farisrfp/smart-pju-device/firmware/interface/pnpm-lock.yaml

lockfileVersion: '6.0'

dependencies:
  '@emotion/react':
    specifier: ^11.7.1
    version: 11.7.1(@babel/core@7.22.1)(react@17.0.2)
  '@emotion/styled':
    specifier: ^11.6.0
    version: 11.6.0(@babel/core@7.22.1)(@emotion/react@11.7.1)(react@17.0.2)
  '@fseehawer/react-circular-slider':
    specifier: ^2.6.1
    version: 2.6.1(global@4.4.0)(react-dom@17.0.2)(react@17.0.2)
  '@headlessui/react':
    specifier: ^1.7.15
    version: 1.7.15(react-dom@17.0.2)(react@17.0.2)
  '@heroicons/react':
    specifier: ^2.0.18
    version: 2.0.18(react@17.0.2)
  '@mui/icons-material':
    specifier: ^5.11.16
    version: 5.11.16(@mui/material@5.2.4)(react@17.0.2)
  '@mui/material':
    specifier: ^5.2.4
    version: 5.2.4(@emotion/react@11.7.1)(@emotion/styled@11.6.0)(react-dom@17.0.2)(react@17.0.2)
  '@testing-library/jest-dom':
    specifier: ^5.16.1
    version: 5.16.1
  '@testing-library/react':
    specifier: ^12.1.2
    version: 12.1.2(react-dom@17.0.2)(react@17.0.2)
  '@testing-library/user-event':
    specifier: ^13.5.0
    version: 13.5.0(@testing-library/dom@9.3.0)
  axios:
    specifier: ^0.27.2
    version: 0.27.2
  react:
    specifier: ^17.0.2
    version: 17.0.2
  react-dom:
    specifier: ^17.0.2
    version: 17.0.2(react@17.0.2)
  react-router-dom:
    specifier: '6'
    version: 6.0.0(react-dom@17.0.2)(react@17.0.2)
  react-scripts:
    specifier: 5.0.0
    version: 5.0.0(@babel/plugin-syntax-flow@7.21.4)(@babel/plugin-transform-react-jsx@7.22.3)(eslint@8.42.0)(react@17.0.2)(typescript@5.1.3)
  replace:
    specifier: ^1.2.1
    version: 1.2.1
  web-vitals:
    specifier: ^2.1.2
    version: 2.1.2
  websocket:
    specifier: ^1.0.34
    version: 1.0.34

devDependencies:
  prettier:
    specifier: ^2.8.8
    version: 2.8.8
  prettier-plugin-tailwindcss:
    specifier: ^0.3.0
    version: 0.3.0(prettier@2.8.8)
  tailwindcss:
    specifier: ^3.3.2
    version: 3.3.2

packages:

  /@alloc/quick-lru@5.2.0:
    resolution: {integrity: sha512-UrcABB+4bUrFABwbluTIBErXwvbsU/V7TZWfmbgJfbkwiBuziS9gxdODUyuiecfdGQ85jglMW6juS3+z5TsKLw==}
    engines: {node: '>=10'}

  /@ampproject/remapping@2.2.1:
    resolution: {integrity: sha512-lFMjJTrFL3j7L9yBxwYfCq2k6qqwHyzuUl/XBnif78PWTJYyL/dfowQHWE3sp6U6ZzqWiiIZnpTMO96zhkjwtg==}
    engines: {node: '>=6.0.0'}
    dependencies:
      '@jridgewell/gen-mapping': 0.3.3
      '@jridgewell/trace-mapping': 0.3.18
    dev: false

  /@apideck/better-ajv-errors@0.3.6(ajv@8.12.0):
    resolution: {integrity: sha512-P+ZygBLZtkp0qqOAJJVX4oX/sFo5JR3eBWwwuqHHhK0GIgQOKWrAfiAaWX0aArHkRWHMuggFEgAZNxVPwPZYaA==}
    engines: {node: '>=10'}
    peerDependencies:
      ajv: '>=8'
    dependencies:
      ajv: 8.12.0
      json-schema: 0.4.0
      jsonpointer: 5.0.1
      leven: 3.1.0
    dev: false

  /@babel/code-frame@7.21.4:
    resolution: {integrity: sha512-LYvhNKfwWSPpocw8GI7gpK2nq3HSDuEPC/uSYaALSJu9xjsalaaYFOq0Pwt5KmVqwEbZlDu81aLXwBOmD/Fv9g==}
    engines: {node: '>=6.9.0'}
    dependencies:
      '@babel/highlight': 7.18.6
    dev: false

  /@babel/compat-data@7.22.3:
    resolution: {integrity: sha512-aNtko9OPOwVESUFp3MZfD8Uzxl7JzSeJpd7npIoxCasU37PFbAQRpKglkaKwlHOyeJdrREpo8TW8ldrkYWwvIQ==}
    engines: {node: '>=6.9.0'}
    dev: false

  /@babel/core@7.22.1:
    resolution: {integrity: sha512-Hkqu7J4ynysSXxmAahpN1jjRwVJ+NdpraFLIWflgjpVob3KNyK3/tIUc7Q7szed8WMp0JNa7Qtd1E9Oo22F9gA==}
    engines: {node: '>=6.9.0'}
    dependencies:
      '@ampproject/remapping': 2.2.1
      '@babel/code-frame': 7.21.4
      '@babel/generator': 7.22.3
      '@babel/helper-compilation-targets': 7.22.1(@babel/core@7.22.1)
      '@babel/helper-module-transforms': 7.22.1
      '@babel/helpers': 7.22.3
      '@babel/parser': 7.22.4
      '@babel/template': 7.21.9
      '@babel/traverse': 7.22.4
      '@babel/types': 7.22.4
      convert-source-map: 1.9.0
      debug: 4.3.4
      gensync: 1.0.0-beta.2
      json5: 2.2.3
      semver: 6.3.0
    transitivePeerDependencies:
      - supports-color
    dev: false

  /@babel/eslint-parser@7.21.8(@babel/core@7.22.1)(eslint@8.42.0):
    resolution: {integrity: sha512-HLhI+2q+BP3sf78mFUZNCGc10KEmoUqtUT1OCdMZsN+qr4qFeLUod62/zAnF3jNQstwyasDkZnVXwfK2Bml7MQ==}
    engines: {node: ^10.13.0 || ^12.13.0 || >=14.0.0}
    peerDependencies:
      '@babel/core': '>=7.11.0'
      eslint: ^7.5.0 || ^8.0.0
    dependencies:
      '@babel/core': 7.22.1
      '@nicolo-ribaudo/eslint-scope-5-internals': 5.1.1-v1
      eslint: 8.42.0
      eslint-visitor-keys: 2.1.0
      semver: 6.3.0
    dev: false

  /@babel/generator@7.22.3:
    resolution: {integrity: sha512-C17MW4wlk//ES/CJDL51kPNwl+qiBQyN7b9SKyVp11BLGFeSPoVaHrv+MNt8jwQFhQWowW88z1eeBx3pFz9v8A==}
    engines: {node: '>=6.9.0'}
    dependencies:
      '@babel/types': 7.22.4
      '@jridgewell/gen-mapping': 0.3.3
      '@jridgewell/trace-mapping': 0.3.18
      jsesc: 2.5.2
    dev: false

  /@babel/helper-annotate-as-pure@7.18.6:
    resolution: {integrity: sha512-duORpUiYrEpzKIop6iNbjnwKLAKnJ47csTyRACyEmWj0QdUrm5aqNJGHSSEQSUAvNW0ojX0dOmK9dZduvkfeXA==}
    engines: {node: '>=6.9.0'}
    dependencies:
      '@babel/types': 7.22.4
    dev: false

  /@babel/helper-builder-binary-assignment-operator-visitor@7.22.3:
    resolution: {integrity: sha512-ahEoxgqNoYXm0k22TvOke48i1PkavGu0qGCmcq9ugi6gnmvKNaMjKBSrZTnWUi1CFEeNAUiVba0Wtzm03aSkJg==}
    engines: {node: '>=6.9.0'}
    dependencies:
      '@babel/types': 7.22.4
    dev: false

  /@babel/helper-compilation-targets@7.22.1(@babel/core@7.22.1):
    resolution: {integrity: sha512-Rqx13UM3yVB5q0D/KwQ8+SPfX/+Rnsy1Lw1k/UwOC4KC6qrzIQoY3lYnBu5EHKBlEHHcj0M0W8ltPSkD8rqfsQ==}
    engines: {node: '>=6.9.0'}
    peerDependencies:
      '@babel/core': ^7.0.0
    dependencies:
      '@babel/compat-data': 7.22.3
      '@babel/core': 7.22.1
      '@babel/helper-validator-option': 7.21.0
      browserslist: 4.21.7
      lru-cache: 5.1.1
      semver: 6.3.0
    dev: false

  /@babel/helper-create-class-features-plugin@7.22.1(@babel/core@7.22.1):
    resolution: {integrity: sha512-SowrZ9BWzYFgzUMwUmowbPSGu6CXL5MSuuCkG3bejahSpSymioPmuLdhPxNOc9MjuNGjy7M/HaXvJ8G82Lywlw==}
    engines: {node: '>=6.9.0'}
    peerDependencies:
      '@babel/core': ^7.0.0
    dependencies:
      '@babel/core': 7.22.1
      '@babel/helper-annotate-as-pure': 7.18.6
      '@babel/helper-environment-visitor': 7.22.1
      '@babel/helper-function-name': 7.21.0
      '@babel/helper-member-expression-to-functions': 7.22.3
      '@babel/helper-optimise-call-expression': 7.18.6
      '@babel/helper-replace-supers': 7.22.1
      '@babel/helper-skip-transparent-expression-wrappers': 7.20.0
      '@babel/helper-split-export-declaration': 7.18.6
      semver: 6.3.0
    transitivePeerDependencies:
      - supports-color
    dev: false

  /@babel/helper-create-regexp-features-plugin@7.22.1(@babel/core@7.22.1):
    resolution: {integrity: sha512-WWjdnfR3LPIe+0EY8td7WmjhytxXtjKAEpnAxun/hkNiyOaPlvGK+NZaBFIdi9ndYV3Gav7BpFvtUwnaJlwi1w==}
    engines: {node: '>=6.9.0'}
    peerDependencies:
      '@babel/core': ^7.0.0
    dependencies:
      '@babel/core': 7.22.1
      '@babel/helper-annotate-as-pure': 7.18.6
      regexpu-core: 5.3.2
      semver: 6.3.0
    dev: false

  /@babel/helper-define-polyfill-provider@0.4.0(@babel/core@7.22.1):
    resolution: {integrity: sha512-RnanLx5ETe6aybRi1cO/edaRH+bNYWaryCEmjDDYyNr4wnSzyOp8T0dWipmqVHKEY3AbVKUom50AKSlj1zmKbg==}
    peerDependencies:
      '@babel/core': ^7.4.0-0
    dependencies:
      '@babel/core': 7.22.1
      '@babel/helper-compilation-targets': 7.22.1(@babel/core@7.22.1)
      '@babel/helper-plugin-utils': 7.21.5
      debug: 4.3.4
      lodash.debounce: 4.0.8
      resolve: 1.22.2
      semver: 6.3.0
    transitivePeerDependencies:
      - supports-color
    dev: false

  /@babel/helper-environment-visitor@7.22.1:
    resolution: {integrity: sha512-Z2tgopurB/kTbidvzeBrc2To3PUP/9i5MUe+fU6QJCQDyPwSH2oRapkLw3KGECDYSjhQZCNxEvNvZlLw8JjGwA==}
    engines: {node: '>=6.9.0'}
    dev: false

  /@babel/helper-function-name@7.21.0:
    resolution: {integrity: sha512-HfK1aMRanKHpxemaY2gqBmL04iAPOPRj7DxtNbiDOrJK+gdwkiNRVpCpUJYbUT+aZyemKN8brqTOxzCaG6ExRg==}
    engines: {node: '>=6.9.0'}
    dependencies:
      '@babel/template': 7.21.9
      '@babel/types': 7.22.4
    dev: false

  /@babel/helper-hoist-variables@7.18.6:
    resolution: {integrity: sha512-UlJQPkFqFULIcyW5sbzgbkxn2FKRgwWiRexcuaR8RNJRy8+LLveqPjwZV/bwrLZCN0eUHD/x8D0heK1ozuoo6Q==}
    engines: {node: '>=6.9.0'}
    dependencies:
      '@babel/types': 7.22.4
    dev: false

  /@babel/helper-member-expression-to-functions@7.22.3:
    resolution: {integrity: sha512-Gl7sK04b/2WOb6OPVeNy9eFKeD3L6++CzL3ykPOWqTn08xgYYK0wz4TUh2feIImDXxcVW3/9WQ1NMKY66/jfZA==}
    engines: {node: '>=6.9.0'}
    dependencies:
      '@babel/types': 7.22.4
    dev: false

  /@babel/helper-module-imports@7.21.4:
    resolution: {integrity: sha512-orajc5T2PsRYUN3ZryCEFeMDYwyw09c/pZeaQEZPH0MpKzSvn3e0uXsDBu3k03VI+9DBiRo+l22BfKTpKwa/Wg==}
    engines: {node: '>=6.9.0'}
    dependencies:
      '@babel/types': 7.22.4
    dev: false

  /@babel/helper-module-transforms@7.22.1:
    resolution: {integrity: sha512-dxAe9E7ySDGbQdCVOY/4+UcD8M9ZFqZcZhSPsPacvCG4M+9lwtDDQfI2EoaSvmf7W/8yCBkGU0m7Pvt1ru3UZw==}
    engines: {node: '>=6.9.0'}
    dependencies:
      '@babel/helper-environment-visitor': 7.22.1
      '@babel/helper-module-imports': 7.21.4
      '@babel/helper-simple-access': 7.21.5
      '@babel/helper-split-export-declaration': 7.18.6
      '@babel/helper-validator-identifier': 7.19.1
      '@babel/template': 7.21.9
      '@babel/traverse': 7.22.4
      '@babel/types': 7.22.4
    transitivePeerDependencies:
      - supports-color
    dev: false

  /@babel/helper-optimise-call-expression@7.18.6:
    resolution: {integrity: sha512-HP59oD9/fEHQkdcbgFCnbmgH5vIQTJbxh2yf+CdM89/glUNnuzr87Q8GIjGEnOktTROemO0Pe0iPAYbqZuOUiA==}
    engines: {node: '>=6.9.0'}
    dependencies:
      '@babel/types': 7.22.4
    dev: false

  /@babel/helper-plugin-utils@7.21.5:
    resolution: {integrity: sha512-0WDaIlXKOX/3KfBK/dwP1oQGiPh6rjMkT7HIRv7i5RR2VUMwrx5ZL0dwBkKx7+SW1zwNdgjHd34IMk5ZjTeHVg==}
    engines: {node: '>=6.9.0'}
    dev: false

  /@babel/helper-remap-async-to-generator@7.18.9(@babel/core@7.22.1):
    resolution: {integrity: sha512-dI7q50YKd8BAv3VEfgg7PS7yD3Rtbi2J1XMXaalXO0W0164hYLnh8zpjRS0mte9MfVp/tltvr/cfdXPvJr1opA==}
    engines: {node: '>=6.9.0'}
    peerDependencies:
      '@babel/core': ^7.0.0
    dependencies:
      '@babel/core': 7.22.1
      '@babel/helper-annotate-as-pure': 7.18.6
      '@babel/helper-environment-visitor': 7.22.1
      '@babel/helper-wrap-function': 7.20.5
      '@babel/types': 7.22.4
    transitivePeerDependencies:
      - supports-color
    dev: false

  /@babel/helper-replace-supers@7.22.1:
    resolution: {integrity: sha512-ut4qrkE4AuSfrwHSps51ekR1ZY/ygrP1tp0WFm8oVq6nzc/hvfV/22JylndIbsf2U2M9LOMwiSddr6y+78j+OQ==}
    engines: {node: '>=6.9.0'}
    dependencies:
      '@babel/helper-environment-visitor': 7.22.1
      '@babel/helper-member-expression-to-functions': 7.22.3
      '@babel/helper-optimise-call-expression': 7.18.6
      '@babel/template': 7.21.9
      '@babel/traverse': 7.22.4
      '@babel/types': 7.22.4
    transitivePeerDependencies:
      - supports-color
    dev: false

  /@babel/helper-simple-access@7.21.5:
    resolution: {integrity: sha512-ENPDAMC1wAjR0uaCUwliBdiSl1KBJAVnMTzXqi64c2MG8MPR6ii4qf7bSXDqSFbr4W6W028/rf5ivoHop5/mkg==}
    engines: {node: '>=6.9.0'}
    dependencies:
      '@babel/types': 7.22.4
    dev: false

  /@babel/helper-skip-transparent-expression-wrappers@7.20.0:
    resolution: {integrity: sha512-5y1JYeNKfvnT8sZcK9DVRtpTbGiomYIHviSP3OQWmDPU3DeH4a1ZlT/N2lyQ5P8egjcRaT/Y9aNqUxK0WsnIIg==}
    engines: {node: '>=6.9.0'}
    dependencies:
      '@babel/types': 7.22.4
    dev: false

  /@babel/helper-split-export-declaration@7.18.6:
    resolution: {integrity: sha512-bde1etTx6ZyTmobl9LLMMQsaizFVZrquTEHOqKeQESMKo4PlObf+8+JA25ZsIpZhT/WEd39+vOdLXAFG/nELpA==}
    engines: {node: '>=6.9.0'}
    dependencies:
      '@babel/types': 7.22.4
    dev: false

  /@babel/helper-string-parser@7.21.5:
    resolution: {integrity: sha512-5pTUx3hAJaZIdW99sJ6ZUUgWq/Y+Hja7TowEnLNMm1VivRgZQL3vpBY3qUACVsvw+yQU6+YgfBVmcbLaZtrA1w==}
    engines: {node: '>=6.9.0'}
    dev: false

  /@babel/helper-validator-identifier@7.19.1:
    resolution: {integrity: sha512-awrNfaMtnHUr653GgGEs++LlAvW6w+DcPrOliSMXWCKo597CwL5Acf/wWdNkf/tfEQE3mjkeD1YOVZOUV/od1w==}
    engines: {node: '>=6.9.0'}
    dev: false

  /@babel/helper-validator-option@7.21.0:
    resolution: {integrity: sha512-rmL/B8/f0mKS2baE9ZpyTcTavvEuWhTTW8amjzXNvYG4AwBsqTLikfXsEofsJEfKHf+HQVQbFOHy6o+4cnC/fQ==}
    engines: {node: '>=6.9.0'}
    dev: false

  /@babel/helper-wrap-function@7.20.5:
    resolution: {integrity: sha512-bYMxIWK5mh+TgXGVqAtnu5Yn1un+v8DDZtqyzKRLUzrh70Eal2O3aZ7aPYiMADO4uKlkzOiRiZ6GX5q3qxvW9Q==}
    engines: {node: '>=6.9.0'}
    dependencies:
      '@babel/helper-function-name': 7.21.0
      '@babel/template': 7.21.9
      '@babel/traverse': 7.22.4
      '@babel/types': 7.22.4
    transitivePeerDependencies:
      - supports-color
    dev: false

  /@babel/helpers@7.22.3:
    resolution: {integrity: sha512-jBJ7jWblbgr7r6wYZHMdIqKc73ycaTcCaWRq4/2LpuPHcx7xMlZvpGQkOYc9HeSjn6rcx15CPlgVcBtZ4WZJ2w==}
    engines: {node: '>=6.9.0'}
    dependencies:
      '@babel/template': 7.21.9
      '@babel/traverse': 7.22.4
      '@babel/types': 7.22.4
    transitivePeerDependencies:
      - supports-color
    dev: false

  /@babel/highlight@7.18.6:
    resolution: {integrity: sha512-u7stbOuYjaPezCuLj29hNW1v64M2Md2qupEKP1fHc7WdOA3DgLh37suiSrZYY7haUB7iBeQZ9P1uiRF359do3g==}
    engines: {node: '>=6.9.0'}
    dependencies:
      '@babel/helper-validator-identifier': 7.19.1
      chalk: 2.4.2
      js-tokens: 4.0.0
    dev: false

  /@babel/parser@7.22.4:
    resolution: {integrity: sha512-VLLsx06XkEYqBtE5YGPwfSGwfrjnyPP5oiGty3S8pQLFDFLaS8VwWSIxkTXpcvr5zeYLE6+MBNl2npl/YnfofA==}
    engines: {node: '>=6.0.0'}
    hasBin: true
    dependencies:
      '@babel/types': 7.22.4
    dev: false

  /@babel/plugin-bugfix-safari-id-destructuring-collision-in-function-expression@7.18.6(@babel/core@7.22.1):
    resolution: {integrity: sha512-Dgxsyg54Fx1d4Nge8UnvTrED63vrwOdPmyvPzlNN/boaliRP54pm3pGzZD1SJUwrBA+Cs/xdG8kXX6Mn/RfISQ==}
    engines: {node: '>=6.9.0'}
    peerDependencies:
      '@babel/core': ^7.0.0
    dependencies:
      '@babel/core': 7.22.1
      '@babel/helper-plugin-utils': 7.21.5
    dev: false

  /@babel/plugin-bugfix-v8-spread-parameters-in-optional-chaining@7.22.3(@babel/core@7.22.1):
    resolution: {integrity: sha512-6r4yRwEnorYByILoDRnEqxtojYKuiIv9FojW2E8GUKo9eWBwbKcd9IiZOZpdyXc64RmyGGyPu3/uAcrz/dq2kQ==}
    engines: {node: '>=6.9.0'}
    peerDependencies:
      '@babel/core': ^7.13.0
    dependencies:
      '@babel/core': 7.22.1
      '@babel/helper-plugin-utils': 7.21.5
      '@babel/helper-skip-transparent-expression-wrappers': 7.20.0
      '@babel/plugin-transform-optional-chaining': 7.22.3(@babel/core@7.22.1)
    dev: false

  /@babel/plugin-proposal-class-properties@7.18.6(@babel/core@7.22.1):
    resolution: {integrity: sha512-cumfXOF0+nzZrrN8Rf0t7M+tF6sZc7vhQwYQck9q1/5w2OExlD+b4v4RpMJFaV1Z7WcDRgO6FqvxqxGlwo+RHQ==}
    engines: {node: '>=6.9.0'}
    peerDependencies:
      '@babel/core': ^7.0.0-0
    dependencies:
      '@babel/core': 7.22.1
      '@babel/helper-create-class-features-plugin': 7.22.1(@babel/core@7.22.1)
      '@babel/helper-plugin-utils': 7.21.5
    transitivePeerDependencies:
      - supports-color
    dev: false

  /@babel/plugin-proposal-decorators@7.22.3(@babel/core@7.22.1):
    resolution: {integrity: sha512-XjTKH3sHr6pPqG+hR1NCdVupwiosfdKM2oSMyKQVQ5Bym9l/p7BuLAqT5U32zZzRCfPq/TPRPzMiiTE9bOXU4w==}
    engines: {node: '>=6.9.0'}
    peerDependencies:
      '@babel/core': ^7.0.0-0
    dependencies:
      '@babel/core': 7.22.1
      '@babel/helper-create-class-features-plugin': 7.22.1(@babel/core@7.22.1)
      '@babel/helper-plugin-utils': 7.21.5
      '@babel/helper-replace-supers': 7.22.1
      '@babel/helper-split-export-declaration': 7.18.6
      '@babel/plugin-syntax-decorators': 7.22.3(@babel/core@7.22.1)
    transitivePeerDependencies:
      - supports-color
    dev: false

  /@babel/plugin-proposal-nullish-coalescing-operator@7.18.6(@babel/core@7.22.1):
    resolution: {integrity: sha512-wQxQzxYeJqHcfppzBDnm1yAY0jSRkUXR2z8RePZYrKwMKgMlE8+Z6LUno+bd6LvbGh8Gltvy74+9pIYkr+XkKA==}
    engines: {node: '>=6.9.0'}
    peerDependencies:
      '@babel/core': ^7.0.0-0
    dependencies:
      '@babel/core': 7.22.1
      '@babel/helper-plugin-utils': 7.21.5
      '@babel/plugin-syntax-nullish-coalescing-operator': 7.8.3(@babel/core@7.22.1)
    dev: false

  /@babel/plugin-proposal-numeric-separator@7.18.6(@babel/core@7.22.1):
    resolution: {integrity: sha512-ozlZFogPqoLm8WBr5Z8UckIoE4YQ5KESVcNudyXOR8uqIkliTEgJ3RoketfG6pmzLdeZF0H/wjE9/cCEitBl7Q==}
    engines: {node: '>=6.9.0'}
    peerDependencies:
      '@babel/core': ^7.0.0-0
    dependencies:
      '@babel/core': 7.22.1
      '@babel/helper-plugin-utils': 7.21.5
      '@babel/plugin-syntax-numeric-separator': 7.10.4(@babel/core@7.22.1)
    dev: false

  /@babel/plugin-proposal-optional-chaining@7.21.0(@babel/core@7.22.1):
    resolution: {integrity: sha512-p4zeefM72gpmEe2fkUr/OnOXpWEf8nAgk7ZYVqqfFiyIG7oFfVZcCrU64hWn5xp4tQ9LkV4bTIa5rD0KANpKNA==}
    engines: {node: '>=6.9.0'}
    peerDependencies:
      '@babel/core': ^7.0.0-0
    dependencies:
      '@babel/core': 7.22.1
      '@babel/helper-plugin-utils': 7.21.5
      '@babel/helper-skip-transparent-expression-wrappers': 7.20.0
      '@babel/plugin-syntax-optional-chaining': 7.8.3(@babel/core@7.22.1)
    dev: false

  /@babel/plugin-proposal-private-methods@7.18.6(@babel/core@7.22.1):
    resolution: {integrity: sha512-nutsvktDItsNn4rpGItSNV2sz1XwS+nfU0Rg8aCx3W3NOKVzdMjJRu0O5OkgDp3ZGICSTbgRpxZoWsxoKRvbeA==}
    engines: {node: '>=6.9.0'}
    peerDependencies:
      '@babel/core': ^7.0.0-0
    dependencies:
      '@babel/core': 7.22.1
      '@babel/helper-create-class-features-plugin': 7.22.1(@babel/core@7.22.1)
      '@babel/helper-plugin-utils': 7.21.5
    transitivePeerDependencies:
      - supports-color
    dev: false

  /@babel/plugin-proposal-private-property-in-object@7.21.11(@babel/core@7.22.1):
    resolution: {integrity: sha512-0QZ8qP/3RLDVBwBFoWAwCtgcDZJVwA5LUJRZU8x2YFfKNuFq161wK3cuGrALu5yiPu+vzwTAg/sMWVNeWeNyaw==}
    engines: {node: '>=6.9.0'}
    peerDependencies:
      '@babel/core': ^7.0.0-0
    dependencies:
      '@babel/core': 7.22.1
      '@babel/helper-annotate-as-pure': 7.18.6
      '@babel/helper-create-class-features-plugin': 7.22.1(@babel/core@7.22.1)
      '@babel/helper-plugin-utils': 7.21.5
      '@babel/plugin-syntax-private-property-in-object': 7.14.5(@babel/core@7.22.1)
    transitivePeerDependencies:
      - supports-color
    dev: false

  /@babel/plugin-proposal-unicode-property-regex@7.18.6(@babel/core@7.22.1):
    resolution: {integrity: sha512-2BShG/d5yoZyXZfVePH91urL5wTG6ASZU9M4o03lKK8u8UW1y08OMttBSOADTcJrnPMpvDXRG3G8fyLh4ovs8w==}
    engines: {node: '>=4'}
    peerDependencies:
      '@babel/core': ^7.0.0-0
    dependencies:
      '@babel/core': 7.22.1
      '@babel/helper-create-regexp-features-plugin': 7.22.1(@babel/core@7.22.1)
      '@babel/helper-plugin-utils': 7.21.5
    dev: false

  /@babel/plugin-syntax-async-generators@7.8.4(@babel/core@7.22.1):
    resolution: {integrity: sha512-tycmZxkGfZaxhMRbXlPXuVFpdWlXpir2W4AMhSJgRKzk/eDlIXOhb2LHWoLpDF7TEHylV5zNhykX6KAgHJmTNw==}
    peerDependencies:
      '@babel/core': ^7.0.0-0
    dependencies:
      '@babel/core': 7.22.1
      '@babel/helper-plugin-utils': 7.21.5
    dev: false

  /@babel/plugin-syntax-bigint@7.8.3(@babel/core@7.22.1):
    resolution: {integrity: sha512-wnTnFlG+YxQm3vDxpGE57Pj0srRU4sHE/mDkt1qv2YJJSeUAec2ma4WLUnUPeKjyrfntVwe/N6dCXpU+zL3Npg==}
    peerDependencies:
      '@babel/core': ^7.0.0-0
    dependencies:
      '@babel/core': 7.22.1
      '@babel/helper-plugin-utils': 7.21.5
    dev: false

  /@babel/plugin-syntax-class-properties@7.12.13(@babel/core@7.22.1):
    resolution: {integrity: sha512-fm4idjKla0YahUNgFNLCB0qySdsoPiZP3iQE3rky0mBUtMZ23yDJ9SJdg6dXTSDnulOVqiF3Hgr9nbXvXTQZYA==}
    peerDependencies:
      '@babel/core': ^7.0.0-0
    dependencies:
      '@babel/core': 7.22.1
      '@babel/helper-plugin-utils': 7.21.5
    dev: false

  /@babel/plugin-syntax-class-static-block@7.14.5(@babel/core@7.22.1):
    resolution: {integrity: sha512-b+YyPmr6ldyNnM6sqYeMWE+bgJcJpO6yS4QD7ymxgH34GBPNDM/THBh8iunyvKIZztiwLH4CJZ0RxTk9emgpjw==}
    engines: {node: '>=6.9.0'}
    peerDependencies:
      '@babel/core': ^7.0.0-0
    dependencies:
      '@babel/core': 7.22.1
      '@babel/helper-plugin-utils': 7.21.5
    dev: false

  /@babel/plugin-syntax-decorators@7.22.3(@babel/core@7.22.1):
    resolution: {integrity: sha512-R16Zuge73+8/nLcDjkIpyhi5wIbN7i7fiuLJR8yQX7vPAa/ltUKtd3iLbb4AgP5nrLi91HnNUNosELIGUGH1bg==}
    engines: {node: '>=6.9.0'}
    peerDependencies:
      '@babel/core': ^7.0.0-0
    dependencies:
      '@babel/core': 7.22.1
      '@babel/helper-plugin-utils': 7.21.5
    dev: false

  /@babel/plugin-syntax-dynamic-import@7.8.3(@babel/core@7.22.1):
    resolution: {integrity: sha512-5gdGbFon+PszYzqs83S3E5mpi7/y/8M9eC90MRTZfduQOYW76ig6SOSPNe41IG5LoP3FGBn2N0RjVDSQiS94kQ==}
    peerDependencies:
      '@babel/core': ^7.0.0-0
    dependencies:
      '@babel/core': 7.22.1
      '@babel/helper-plugin-utils': 7.21.5
    dev: false

  /@babel/plugin-syntax-export-namespace-from@7.8.3(@babel/core@7.22.1):
    resolution: {integrity: sha512-MXf5laXo6c1IbEbegDmzGPwGNTsHZmEy6QGznu5Sh2UCWvueywb2ee+CCE4zQiZstxU9BMoQO9i6zUFSY0Kj0Q==}
    peerDependencies:
      '@babel/core': ^7.0.0-0
    dependencies:
      '@babel/core': 7.22.1
      '@babel/helper-plugin-utils': 7.21.5
    dev: false

  /@babel/plugin-syntax-flow@7.21.4(@babel/core@7.22.1):
    resolution: {integrity: sha512-l9xd3N+XG4fZRxEP3vXdK6RW7vN1Uf5dxzRC/09wV86wqZ/YYQooBIGNsiRdfNR3/q2/5pPzV4B54J/9ctX5jw==}
    engines: {node: '>=6.9.0'}
    peerDependencies:
      '@babel/core': ^7.0.0-0
    dependencies:
      '@babel/core': 7.22.1
      '@babel/helper-plugin-utils': 7.21.5
    dev: false

  /@babel/plugin-syntax-import-assertions@7.20.0(@babel/core@7.22.1):
    resolution: {integrity: sha512-IUh1vakzNoWalR8ch/areW7qFopR2AEw03JlG7BbrDqmQ4X3q9uuipQwSGrUn7oGiemKjtSLDhNtQHzMHr1JdQ==}
    engines: {node: '>=6.9.0'}
    peerDependencies:
      '@babel/core': ^7.0.0-0
    dependencies:
      '@babel/core': 7.22.1
      '@babel/helper-plugin-utils': 7.21.5
    dev: false

  /@babel/plugin-syntax-import-attributes@7.22.3(@babel/core@7.22.1):
    resolution: {integrity: sha512-i35jZJv6aO7hxEbIWQ41adVfOzjm9dcYDNeWlBMd8p0ZQRtNUCBrmGwZt+H5lb+oOC9a3svp956KP0oWGA1YsA==}
    engines: {node: '>=6.9.0'}
    peerDependencies:
      '@babel/core': ^7.0.0-0
    dependencies:
      '@babel/core': 7.22.1
      '@babel/helper-plugin-utils': 7.21.5
    dev: false

  /@babel/plugin-syntax-import-meta@7.10.4(@babel/core@7.22.1):
    resolution: {integrity: sha512-Yqfm+XDx0+Prh3VSeEQCPU81yC+JWZ2pDPFSS4ZdpfZhp4MkFMaDC1UqseovEKwSUpnIL7+vK+Clp7bfh0iD7g==}
    peerDependencies:
      '@babel/core': ^7.0.0-0
    dependencies:
      '@babel/core': 7.22.1
      '@babel/helper-plugin-utils': 7.21.5
    dev: false

  /@babel/plugin-syntax-json-strings@7.8.3(@babel/core@7.22.1):
    resolution: {integrity: sha512-lY6kdGpWHvjoe2vk4WrAapEuBR69EMxZl+RoGRhrFGNYVK8mOPAW8VfbT/ZgrFbXlDNiiaxQnAtgVCZ6jv30EA==}
    peerDependencies:
      '@babel/core': ^7.0.0-0
    dependencies:
      '@babel/core': 7.22.1
      '@babel/helper-plugin-utils': 7.21.5
    dev: false

  /@babel/plugin-syntax-jsx@7.21.4(@babel/core@7.22.1):
    resolution: {integrity: sha512-5hewiLct5OKyh6PLKEYaFclcqtIgCb6bmELouxjF6up5q3Sov7rOayW4RwhbaBL0dit8rA80GNfY+UuDp2mBbQ==}
    engines: {node: '>=6.9.0'}
    peerDependencies:
      '@babel/core': ^7.0.0-0
    dependencies:
      '@babel/core': 7.22.1
      '@babel/helper-plugin-utils': 7.21.5
    dev: false

  /@babel/plugin-syntax-logical-assignment-operators@7.10.4(@babel/core@7.22.1):
    resolution: {integrity: sha512-d8waShlpFDinQ5MtvGU9xDAOzKH47+FFoney2baFIoMr952hKOLp1HR7VszoZvOsV/4+RRszNY7D17ba0te0ig==}
    peerDependencies:
      '@babel/core': ^7.0.0-0
    dependencies:
      '@babel/core': 7.22.1
      '@babel/helper-plugin-utils': 7.21.5
    dev: false

  /@babel/plugin-syntax-nullish-coalescing-operator@7.8.3(@babel/core@7.22.1):
    resolution: {integrity: sha512-aSff4zPII1u2QD7y+F8oDsz19ew4IGEJg9SVW+bqwpwtfFleiQDMdzA/R+UlWDzfnHFCxxleFT0PMIrR36XLNQ==}
    peerDependencies:
      '@babel/core': ^7.0.0-0
    dependencies:
      '@babel/core': 7.22.1
      '@babel/helper-plugin-utils': 7.21.5
    dev: false

  /@babel/plugin-syntax-numeric-separator@7.10.4(@babel/core@7.22.1):
    resolution: {integrity: sha512-9H6YdfkcK/uOnY/K7/aA2xpzaAgkQn37yzWUMRK7OaPOqOpGS1+n0H5hxT9AUw9EsSjPW8SVyMJwYRtWs3X3ug==}
    peerDependencies:
      '@babel/core': ^7.0.0-0
    dependencies:
      '@babel/core': 7.22.1
      '@babel/helper-plugin-utils': 7.21.5
    dev: false

  /@babel/plugin-syntax-object-rest-spread@7.8.3(@babel/core@7.22.1):
    resolution: {integrity: sha512-XoqMijGZb9y3y2XskN+P1wUGiVwWZ5JmoDRwx5+3GmEplNyVM2s2Dg8ILFQm8rWM48orGy5YpI5Bl8U1y7ydlA==}
    peerDependencies:
      '@babel/core': ^7.0.0-0
    dependencies:
      '@babel/core': 7.22.1
      '@babel/helper-plugin-utils': 7.21.5
    dev: false

  /@babel/plugin-syntax-optional-catch-binding@7.8.3(@babel/core@7.22.1):
    resolution: {integrity: sha512-6VPD0Pc1lpTqw0aKoeRTMiB+kWhAoT24PA+ksWSBrFtl5SIRVpZlwN3NNPQjehA2E/91FV3RjLWoVTglWcSV3Q==}
    peerDependencies:
      '@babel/core': ^7.0.0-0
    dependencies:
      '@babel/core': 7.22.1
      '@babel/helper-plugin-utils': 7.21.5
    dev: false

  /@babel/plugin-syntax-optional-chaining@7.8.3(@babel/core@7.22.1):
    resolution: {integrity: sha512-KoK9ErH1MBlCPxV0VANkXW2/dw4vlbGDrFgz8bmUsBGYkFRcbRwMh6cIJubdPrkxRwuGdtCk0v/wPTKbQgBjkg==}
    peerDependencies:
      '@babel/core': ^7.0.0-0
    dependencies:
      '@babel/core': 7.22.1
      '@babel/helper-plugin-utils': 7.21.5
    dev: false

  /@babel/plugin-syntax-private-property-in-object@7.14.5(@babel/core@7.22.1):
    resolution: {integrity: sha512-0wVnp9dxJ72ZUJDV27ZfbSj6iHLoytYZmh3rFcxNnvsJF3ktkzLDZPy/mA17HGsaQT3/DQsWYX1f1QGWkCoVUg==}
    engines: {node: '>=6.9.0'}
    peerDependencies:
      '@babel/core': ^7.0.0-0
    dependencies:
      '@babel/core': 7.22.1
      '@babel/helper-plugin-utils': 7.21.5
    dev: false

  /@babel/plugin-syntax-top-level-await@7.14.5(@babel/core@7.22.1):
    resolution: {integrity: sha512-hx++upLv5U1rgYfwe1xBQUhRmU41NEvpUvrp8jkrSCdvGSnM5/qdRMtylJ6PG5OFkBaHkbTAKTnd3/YyESRHFw==}
    engines: {node: '>=6.9.0'}
    peerDependencies:
      '@babel/core': ^7.0.0-0
    dependencies:
      '@babel/core': 7.22.1
      '@babel/helper-plugin-utils': 7.21.5
    dev: false

  /@babel/plugin-syntax-typescript@7.21.4(@babel/core@7.22.1):
    resolution: {integrity: sha512-xz0D39NvhQn4t4RNsHmDnnsaQizIlUkdtYvLs8La1BlfjQ6JEwxkJGeqJMW2tAXx+q6H+WFuUTXNdYVpEya0YA==}
    engines: {node: '>=6.9.0'}
    peerDependencies:
      '@babel/core': ^7.0.0-0
    dependencies:
      '@babel/core': 7.22.1
      '@babel/helper-plugin-utils': 7.21.5
    dev: false

  /@babel/plugin-syntax-unicode-sets-regex@7.18.6(@babel/core@7.22.1):
    resolution: {integrity: sha512-727YkEAPwSIQTv5im8QHz3upqp92JTWhidIC81Tdx4VJYIte/VndKf1qKrfnnhPLiPghStWfvC/iFaMCQu7Nqg==}
    engines: {node: '>=6.9.0'}
    peerDependencies:
      '@babel/core': ^7.0.0
    dependencies:
      '@babel/core': 7.22.1
      '@babel/helper-create-regexp-features-plugin': 7.22.1(@babel/core@7.22.1)
      '@babel/helper-plugin-utils': 7.21.5
    dev: false

  /@babel/plugin-transform-arrow-functions@7.21.5(@babel/core@7.22.1):
    resolution: {integrity: sha512-wb1mhwGOCaXHDTcsRYMKF9e5bbMgqwxtqa2Y1ifH96dXJPwbuLX9qHy3clhrxVqgMz7nyNXs8VkxdH8UBcjKqA==}
    engines: {node: '>=6.9.0'}
    peerDependencies:
      '@babel/core': ^7.0.0-0
    dependencies:
      '@babel/core': 7.22.1
      '@babel/helper-plugin-utils': 7.21.5
    dev: false

  /@babel/plugin-transform-async-generator-functions@7.22.3(@babel/core@7.22.1):
    resolution: {integrity: sha512-36A4Aq48t66btydbZd5Fk0/xJqbpg/v4QWI4AH4cYHBXy9Mu42UOupZpebKFiCFNT9S9rJFcsld0gsv0ayLjtA==}
    engines: {node: '>=6.9.0'}
    peerDependencies:
      '@babel/core': ^7.0.0-0
    dependencies:
      '@babel/core': 7.22.1
      '@babel/helper-environment-visitor': 7.22.1
      '@babel/helper-plugin-utils': 7.21.5
      '@babel/helper-remap-async-to-generator': 7.18.9(@babel/core@7.22.1)
      '@babel/plugin-syntax-async-generators': 7.8.4(@babel/core@7.22.1)
    transitivePeerDependencies:
      - supports-color
    dev: false

  /@babel/plugin-transform-async-to-generator@7.20.7(@babel/core@7.22.1):
    resolution: {integrity: sha512-Uo5gwHPT9vgnSXQxqGtpdufUiWp96gk7yiP4Mp5bm1QMkEmLXBO7PAGYbKoJ6DhAwiNkcHFBol/x5zZZkL/t0Q==}
    engines: {node: '>=6.9.0'}
    peerDependencies:
      '@babel/core': ^7.0.0-0
    dependencies:
      '@babel/core': 7.22.1
      '@babel/helper-module-imports': 7.21.4
      '@babel/helper-plugin-utils': 7.21.5
      '@babel/helper-remap-async-to-generator': 7.18.9(@babel/core@7.22.1)
    transitivePeerDependencies:
      - supports-color
    dev: false

  /@babel/plugin-transform-block-scoped-functions@7.18.6(@babel/core@7.22.1):
    resolution: {integrity: sha512-ExUcOqpPWnliRcPqves5HJcJOvHvIIWfuS4sroBUenPuMdmW+SMHDakmtS7qOo13sVppmUijqeTv7qqGsvURpQ==}
    engines: {node: '>=6.9.0'}
    peerDependencies:
      '@babel/core': ^7.0.0-0
    dependencies:
      '@babel/core': 7.22.1
      '@babel/helper-plugin-utils': 7.21.5
    dev: false

  /@babel/plugin-transform-block-scoping@7.21.0(@babel/core@7.22.1):
    resolution: {integrity: sha512-Mdrbunoh9SxwFZapeHVrwFmri16+oYotcZysSzhNIVDwIAb1UV+kvnxULSYq9J3/q5MDG+4X6w8QVgD1zhBXNQ==}
    engines: {node: '>=6.9.0'}
    peerDependencies:
      '@babel/core': ^7.0.0-0
    dependencies:
      '@babel/core': 7.22.1
      '@babel/helper-plugin-utils': 7.21.5
    dev: false

  /@babel/plugin-transform-class-properties@7.22.3(@babel/core@7.22.1):
    resolution: {integrity: sha512-mASLsd6rhOrLZ5F3WbCxkzl67mmOnqik0zrg5W6D/X0QMW7HtvnoL1dRARLKIbMP3vXwkwziuLesPqWVGIl6Bw==}
    engines: {node: '>=6.9.0'}
    peerDependencies:
      '@babel/core': ^7.0.0-0
    dependencies:
      '@babel/core': 7.22.1
      '@babel/helper-create-class-features-plugin': 7.22.1(@babel/core@7.22.1)
      '@babel/helper-plugin-utils': 7.21.5
    transitivePeerDependencies:
      - supports-color
    dev: false

  /@babel/plugin-transform-class-static-block@7.22.3(@babel/core@7.22.1):
    resolution: {integrity: sha512-5BirgNWNOx7cwbTJCOmKFJ1pZjwk5MUfMIwiBBvsirCJMZeQgs5pk6i1OlkVg+1Vef5LfBahFOrdCnAWvkVKMw==}
    engines: {node: '>=6.9.0'}
    peerDependencies:
      '@babel/core': ^7.12.0
    dependencies:
      '@babel/core': 7.22.1
      '@babel/helper-create-class-features-plugin': 7.22.1(@babel/core@7.22.1)
      '@babel/helper-plugin-utils': 7.21.5
      '@babel/plugin-syntax-class-static-block': 7.14.5(@babel/core@7.22.1)
    transitivePeerDependencies:
      - supports-color
    dev: false

  /@babel/plugin-transform-classes@7.21.0(@babel/core@7.22.1):
    resolution: {integrity: sha512-RZhbYTCEUAe6ntPehC4hlslPWosNHDox+vAs4On/mCLRLfoDVHf6hVEd7kuxr1RnHwJmxFfUM3cZiZRmPxJPXQ==}
    engines: {node: '>=6.9.0'}
    peerDependencies:
      '@babel/core': ^7.0.0-0
    dependencies:
      '@babel/core': 7.22.1
      '@babel/helper-annotate-as-pure': 7.18.6
      '@babel/helper-compilation-targets': 7.22.1(@babel/core@7.22.1)
      '@babel/helper-environment-visitor': 7.22.1
      '@babel/helper-function-name': 7.21.0
      '@babel/helper-optimise-call-expression': 7.18.6
      '@babel/helper-plugin-utils': 7.21.5
      '@babel/helper-replace-supers': 7.22.1
      '@babel/helper-split-export-declaration': 7.18.6
      globals: 11.12.0
    transitivePeerDependencies:
      - supports-color
    dev: false

  /@babel/plugin-transform-computed-properties@7.21.5(@babel/core@7.22.1):
    resolution: {integrity: sha512-TR653Ki3pAwxBxUe8srfF3e4Pe3FTA46uaNHYyQwIoM4oWKSoOZiDNyHJ0oIoDIUPSRQbQG7jzgVBX3FPVne1Q==}
    engines: {node: '>=6.9.0'}
    peerDependencies:
      '@babel/core': ^7.0.0-0
    dependencies:
      '@babel/core': 7.22.1
      '@babel/helper-plugin-utils': 7.21.5
      '@babel/template': 7.21.9
    dev: false

  /@babel/plugin-transform-destructuring@7.21.3(@babel/core@7.22.1):
    resolution: {integrity: sha512-bp6hwMFzuiE4HqYEyoGJ/V2LeIWn+hLVKc4pnj++E5XQptwhtcGmSayM029d/j2X1bPKGTlsyPwAubuU22KhMA==}
    engines: {node: '>=6.9.0'}
    peerDependencies:
      '@babel/core': ^7.0.0-0
    dependencies:
      '@babel/core': 7.22.1
      '@babel/helper-plugin-utils': 7.21.5
    dev: false

  /@babel/plugin-transform-dotall-regex@7.18.6(@babel/core@7.22.1):
    resolution: {integrity: sha512-6S3jpun1eEbAxq7TdjLotAsl4WpQI9DxfkycRcKrjhQYzU87qpXdknpBg/e+TdcMehqGnLFi7tnFUBR02Vq6wg==}
    engines: {node: '>=6.9.0'}
    peerDependencies:
      '@babel/core': ^7.0.0-0
    dependencies:
      '@babel/core': 7.22.1
      '@babel/helper-create-regexp-features-plugin': 7.22.1(@babel/core@7.22.1)
      '@babel/helper-plugin-utils': 7.21.5
    dev: false

  /@babel/plugin-transform-duplicate-keys@7.18.9(@babel/core@7.22.1):
    resolution: {integrity: sha512-d2bmXCtZXYc59/0SanQKbiWINadaJXqtvIQIzd4+hNwkWBgyCd5F/2t1kXoUdvPMrxzPvhK6EMQRROxsue+mfw==}
    engines: {node: '>=6.9.0'}
    peerDependencies:
      '@babel/core': ^7.0.0-0
    dependencies:
      '@babel/core': 7.22.1
      '@babel/helper-plugin-utils': 7.21.5
    dev: false

  /@babel/plugin-transform-dynamic-import@7.22.1(@babel/core@7.22.1):
    resolution: {integrity: sha512-rlhWtONnVBPdmt+jeewS0qSnMz/3yLFrqAP8hHC6EDcrYRSyuz9f9yQhHvVn2Ad6+yO9fHXac5piudeYrInxwQ==}
    engines: {node: '>=6.9.0'}
    peerDependencies:
      '@babel/core': ^7.0.0-0
    dependencies:
      '@babel/core': 7.22.1
      '@babel/helper-plugin-utils': 7.21.5
      '@babel/plugin-syntax-dynamic-import': 7.8.3(@babel/core@7.22.1)
    dev: false

  /@babel/plugin-transform-exponentiation-operator@7.18.6(@babel/core@7.22.1):
    resolution: {integrity: sha512-wzEtc0+2c88FVR34aQmiz56dxEkxr2g8DQb/KfaFa1JYXOFVsbhvAonFN6PwVWj++fKmku8NP80plJ5Et4wqHw==}
    engines: {node: '>=6.9.0'}
    peerDependencies:
      '@babel/core': ^7.0.0-0
    dependencies:
      '@babel/core': 7.22.1
      '@babel/helper-builder-binary-assignment-operator-visitor': 7.22.3
      '@babel/helper-plugin-utils': 7.21.5
    dev: false

  /@babel/plugin-transform-export-namespace-from@7.22.3(@babel/core@7.22.1):
    resolution: {integrity: sha512-5Ti1cHLTDnt3vX61P9KZ5IG09bFXp4cDVFJIAeCZuxu9OXXJJZp5iP0n/rzM2+iAutJY+KWEyyHcRaHlpQ/P5g==}
    engines: {node: '>=6.9.0'}
    peerDependencies:
      '@babel/core': ^7.0.0-0
    dependencies:
      '@babel/core': 7.22.1
      '@babel/helper-plugin-utils': 7.21.5
      '@babel/plugin-syntax-export-namespace-from': 7.8.3(@babel/core@7.22.1)
    dev: false

  /@babel/plugin-transform-flow-strip-types@7.21.0(@babel/core@7.22.1):
    resolution: {integrity: sha512-FlFA2Mj87a6sDkW4gfGrQQqwY/dLlBAyJa2dJEZ+FHXUVHBflO2wyKvg+OOEzXfrKYIa4HWl0mgmbCzt0cMb7w==}
    engines: {node: '>=6.9.0'}
    peerDependencies:
      '@babel/core': ^7.0.0-0
    dependencies:
      '@babel/core': 7.22.1
      '@babel/helper-plugin-utils': 7.21.5
      '@babel/plugin-syntax-flow': 7.21.4(@babel/core@7.22.1)
    dev: false

  /@babel/plugin-transform-for-of@7.21.5(@babel/core@7.22.1):
    resolution: {integrity: sha512-nYWpjKW/7j/I/mZkGVgHJXh4bA1sfdFnJoOXwJuj4m3Q2EraO/8ZyrkCau9P5tbHQk01RMSt6KYLCsW7730SXQ==}
    engines: {node: '>=6.9.0'}
    peerDependencies:
      '@babel/core': ^7.0.0-0
    dependencies:
      '@babel/core': 7.22.1
      '@babel/helper-plugin-utils': 7.21.5
    dev: false

  /@babel/plugin-transform-function-name@7.18.9(@babel/core@7.22.1):
    resolution: {integrity: sha512-WvIBoRPaJQ5yVHzcnJFor7oS5Ls0PYixlTYE63lCj2RtdQEl15M68FXQlxnG6wdraJIXRdR7KI+hQ7q/9QjrCQ==}
    engines: {node: '>=6.9.0'}
    peerDependencies:
      '@babel/core': ^7.0.0-0
    dependencies:
      '@babel/core': 7.22.1
      '@babel/helper-compilation-targets': 7.22.1(@babel/core@7.22.1)
      '@babel/helper-function-name': 7.21.0
      '@babel/helper-plugin-utils': 7.21.5
    dev: false

  /@babel/plugin-transform-json-strings@7.22.3(@babel/core@7.22.1):
    resolution: {integrity: sha512-IuvOMdeOOY2X4hRNAT6kwbePtK21BUyrAEgLKviL8pL6AEEVUVcqtRdN/HJXBLGIbt9T3ETmXRnFedRRmQNTYw==}
    engines: {node: '>=6.9.0'}
    peerDependencies:
      '@babel/core': ^7.0.0-0
    dependencies:
      '@babel/core': 7.22.1
      '@babel/helper-plugin-utils': 7.21.5
      '@babel/plugin-syntax-json-strings': 7.8.3(@babel/core@7.22.1)
    dev: false

  /@babel/plugin-transform-literals@7.18.9(@babel/core@7.22.1):
    resolution: {integrity: sha512-IFQDSRoTPnrAIrI5zoZv73IFeZu2dhu6irxQjY9rNjTT53VmKg9fenjvoiOWOkJ6mm4jKVPtdMzBY98Fp4Z4cg==}
    engines: {node: '>=6.9.0'}
    peerDependencies:
      '@babel/core': ^7.0.0-0
    dependencies:
      '@babel/core': 7.22.1
      '@babel/helper-plugin-utils': 7.21.5
    dev: false

  /@babel/plugin-transform-logical-assignment-operators@7.22.3(@babel/core@7.22.1):
    resolution: {integrity: sha512-CbayIfOw4av2v/HYZEsH+Klks3NC2/MFIR3QR8gnpGNNPEaq2fdlVCRYG/paKs7/5hvBLQ+H70pGWOHtlNEWNA==}
    engines: {node: '>=6.9.0'}
    peerDependencies:
      '@babel/core': ^7.0.0-0
    dependencies:
      '@babel/core': 7.22.1
      '@babel/helper-plugin-utils': 7.21.5
      '@babel/plugin-syntax-logical-assignment-operators': 7.10.4(@babel/core@7.22.1)
    dev: false

  /@babel/plugin-transform-member-expression-literals@7.18.6(@babel/core@7.22.1):
    resolution: {integrity: sha512-qSF1ihLGO3q+/g48k85tUjD033C29TNTVB2paCwZPVmOsjn9pClvYYrM2VeJpBY2bcNkuny0YUyTNRyRxJ54KA==}
    engines: {node: '>=6.9.0'}
    peerDependencies:
      '@babel/core': ^7.0.0-0
    dependencies:
      '@babel/core': 7.22.1
      '@babel/helper-plugin-utils': 7.21.5
    dev: false

  /@babel/plugin-transform-modules-amd@7.20.11(@babel/core@7.22.1):
    resolution: {integrity: sha512-NuzCt5IIYOW0O30UvqktzHYR2ud5bOWbY0yaxWZ6G+aFzOMJvrs5YHNikrbdaT15+KNO31nPOy5Fim3ku6Zb5g==}
    engines: {node: '>=6.9.0'}
    peerDependencies:
      '@babel/core': ^7.0.0-0
    dependencies:
      '@babel/core': 7.22.1
      '@babel/helper-module-transforms': 7.22.1
      '@babel/helper-plugin-utils': 7.21.5
    transitivePeerDependencies:
      - supports-color
    dev: false

  /@babel/plugin-transform-modules-commonjs@7.21.5(@babel/core@7.22.1):
    resolution: {integrity: sha512-OVryBEgKUbtqMoB7eG2rs6UFexJi6Zj6FDXx+esBLPTCxCNxAY9o+8Di7IsUGJ+AVhp5ncK0fxWUBd0/1gPhrQ==}
    engines: {node: '>=6.9.0'}
    peerDependencies:
      '@babel/core': ^7.0.0-0
    dependencies:
      '@babel/core': 7.22.1
      '@babel/helper-module-transforms': 7.22.1
      '@babel/helper-plugin-utils': 7.21.5
      '@babel/helper-simple-access': 7.21.5
    transitivePeerDependencies:
      - supports-color
    dev: false

  /@babel/plugin-transform-modules-systemjs@7.22.3(@babel/core@7.22.1):
    resolution: {integrity: sha512-V21W3bKLxO3ZjcBJZ8biSvo5gQ85uIXW2vJfh7JSWf/4SLUSr1tOoHX3ruN4+Oqa2m+BKfsxTR1I+PsvkIWvNw==}
    engines: {node: '>=6.9.0'}
    peerDependencies:
      '@babel/core': ^7.0.0-0
    dependencies:
      '@babel/core': 7.22.1
      '@babel/helper-hoist-variables': 7.18.6
      '@babel/helper-module-transforms': 7.22.1
      '@babel/helper-plugin-utils': 7.21.5
      '@babel/helper-validator-identifier': 7.19.1
    transitivePeerDependencies:
      - supports-color
    dev: false

  /@babel/plugin-transform-modules-umd@7.18.6(@babel/core@7.22.1):
    resolution: {integrity: sha512-dcegErExVeXcRqNtkRU/z8WlBLnvD4MRnHgNs3MytRO1Mn1sHRyhbcpYbVMGclAqOjdW+9cfkdZno9dFdfKLfQ==}
    engines: {node: '>=6.9.0'}
    peerDependencies:
      '@babel/core': ^7.0.0-0
    dependencies:
      '@babel/core': 7.22.1
      '@babel/helper-module-transforms': 7.22.1
      '@babel/helper-plugin-utils': 7.21.5
    transitivePeerDependencies:
      - supports-color
    dev: false

  /@babel/plugin-transform-named-capturing-groups-regex@7.22.3(@babel/core@7.22.1):
    resolution: {integrity: sha512-c6HrD/LpUdNNJsISQZpds3TXvfYIAbo+efE9aWmY/PmSRD0agrJ9cPMt4BmArwUQ7ZymEWTFjTyp+yReLJZh0Q==}
    engines: {node: '>=6.9.0'}
    peerDependencies:
      '@babel/core': ^7.0.0
    dependencies:
      '@babel/core': 7.22.1
      '@babel/helper-create-regexp-features-plugin': 7.22.1(@babel/core@7.22.1)
      '@babel/helper-plugin-utils': 7.21.5
    dev: false

  /@babel/plugin-transform-new-target@7.22.3(@babel/core@7.22.1):
    resolution: {integrity: sha512-5RuJdSo89wKdkRTqtM9RVVJzHum9c2s0te9rB7vZC1zKKxcioWIy+xcu4OoIAjyFZhb/bp5KkunuLin1q7Ct+w==}
    engines: {node: '>=6.9.0'}
    peerDependencies:
      '@babel/core': ^7.0.0-0
    dependencies:
      '@babel/core': 7.22.1
      '@babel/helper-plugin-utils': 7.21.5
    dev: false

  /@babel/plugin-transform-nullish-coalescing-operator@7.22.3(@babel/core@7.22.1):
    resolution: {integrity: sha512-CpaoNp16nX7ROtLONNuCyenYdY/l7ZsR6aoVa7rW7nMWisoNoQNIH5Iay/4LDyRjKMuElMqXiBoOQCDLTMGZiw==}
    engines: {node: '>=6.9.0'}
    peerDependencies:
      '@babel/core': ^7.0.0-0
    dependencies:
      '@babel/core': 7.22.1
      '@babel/helper-plugin-utils': 7.21.5
      '@babel/plugin-syntax-nullish-coalescing-operator': 7.8.3(@babel/core@7.22.1)
    dev: false

  /@babel/plugin-transform-numeric-separator@7.22.3(@babel/core@7.22.1):
    resolution: {integrity: sha512-+AF88fPDJrnseMh5vD9+SH6wq4ZMvpiTMHh58uLs+giMEyASFVhcT3NkoyO+NebFCNnpHJEq5AXO2txV4AGPDQ==}
    engines: {node: '>=6.9.0'}
    peerDependencies:
      '@babel/core': ^7.0.0-0
    dependencies:
      '@babel/core': 7.22.1
      '@babel/helper-plugin-utils': 7.21.5
      '@babel/plugin-syntax-numeric-separator': 7.10.4(@babel/core@7.22.1)
    dev: false

  /@babel/plugin-transform-object-rest-spread@7.22.3(@babel/core@7.22.1):
    resolution: {integrity: sha512-38bzTsqMMCI46/TQnJwPPpy33EjLCc1Gsm2hRTF6zTMWnKsN61vdrpuzIEGQyKEhDSYDKyZHrrd5FMj4gcUHhw==}
    engines: {node: '>=6.9.0'}
    peerDependencies:
      '@babel/core': ^7.0.0-0
    dependencies:
      '@babel/compat-data': 7.22.3
      '@babel/core': 7.22.1
      '@babel/helper-compilation-targets': 7.22.1(@babel/core@7.22.1)
      '@babel/helper-plugin-utils': 7.21.5
      '@babel/plugin-syntax-object-rest-spread': 7.8.3(@babel/core@7.22.1)
      '@babel/plugin-transform-parameters': 7.22.3(@babel/core@7.22.1)
    dev: false

  /@babel/plugin-transform-object-super@7.18.6(@babel/core@7.22.1):
    resolution: {integrity: sha512-uvGz6zk+pZoS1aTZrOvrbj6Pp/kK2mp45t2B+bTDre2UgsZZ8EZLSJtUg7m/no0zOJUWgFONpB7Zv9W2tSaFlA==}
    engines: {node: '>=6.9.0'}
    peerDependencies:
      '@babel/core': ^7.0.0-0
    dependencies:
      '@babel/core': 7.22.1
      '@babel/helper-plugin-utils': 7.21.5
      '@babel/helper-replace-supers': 7.22.1
    transitivePeerDependencies:
      - supports-color
    dev: false

  /@babel/plugin-transform-optional-catch-binding@7.22.3(@babel/core@7.22.1):
    resolution: {integrity: sha512-bnDFWXFzWY0BsOyqaoSXvMQ2F35zutQipugog/rqotL2S4ciFOKlRYUu9djt4iq09oh2/34hqfRR2k1dIvuu4g==}
    engines: {node: '>=6.9.0'}
    peerDependencies:
      '@babel/core': ^7.0.0-0
    dependencies:
      '@babel/core': 7.22.1
      '@babel/helper-plugin-utils': 7.21.5
      '@babel/plugin-syntax-optional-catch-binding': 7.8.3(@babel/core@7.22.1)
    dev: false

  /@babel/plugin-transform-optional-chaining@7.22.3(@babel/core@7.22.1):
    resolution: {integrity: sha512-63v3/UFFxhPKT8j8u1jTTGVyITxl7/7AfOqK8C5gz1rHURPUGe3y5mvIf68eYKGoBNahtJnTxBKug4BQOnzeJg==}
    engines: {node: '>=6.9.0'}
    peerDependencies:
      '@babel/core': ^7.0.0-0
    dependencies:
      '@babel/core': 7.22.1
      '@babel/helper-plugin-utils': 7.21.5
      '@babel/helper-skip-transparent-expression-wrappers': 7.20.0
      '@babel/plugin-syntax-optional-chaining': 7.8.3(@babel/core@7.22.1)
    dev: false

  /@babel/plugin-transform-parameters@7.22.3(@babel/core@7.22.1):
    resolution: {integrity: sha512-x7QHQJHPuD9VmfpzboyGJ5aHEr9r7DsAsdxdhJiTB3J3j8dyl+NFZ+rX5Q2RWFDCs61c06qBfS4ys2QYn8UkMw==}
    engines: {node: '>=6.9.0'}
    peerDependencies:
      '@babel/core': ^7.0.0-0
    dependencies:
      '@babel/core': 7.22.1
      '@babel/helper-plugin-utils': 7.21.5
    dev: false

  /@babel/plugin-transform-private-methods@7.22.3(@babel/core@7.22.1):
    resolution: {integrity: sha512-fC7jtjBPFqhqpPAE+O4LKwnLq7gGkD3ZmC2E3i4qWH34mH3gOg2Xrq5YMHUq6DM30xhqM1DNftiRaSqVjEG+ug==}
    engines: {node: '>=6.9.0'}
    peerDependencies:
      '@babel/core': ^7.0.0-0
    dependencies:
      '@babel/core': 7.22.1
      '@babel/helper-create-class-features-plugin': 7.22.1(@babel/core@7.22.1)
      '@babel/helper-plugin-utils': 7.21.5
    transitivePeerDependencies:
      - supports-color
    dev: false

  /@babel/plugin-transform-private-property-in-object@7.22.3(@babel/core@7.22.1):
    resolution: {integrity: sha512-C7MMl4qWLpgVCbXfj3UW8rR1xeCnisQ0cU7YJHV//8oNBS0aCIVg1vFnZXxOckHhEpQyqNNkWmvSEWnMLlc+Vw==}
    engines: {node: '>=6.9.0'}
    peerDependencies:
      '@babel/core': ^7.0.0-0
    dependencies:
      '@babel/core': 7.22.1
      '@babel/helper-annotate-as-pure': 7.18.6
      '@babel/helper-create-class-features-plugin': 7.22.1(@babel/core@7.22.1)
      '@babel/helper-plugin-utils': 7.21.5
      '@babel/plugin-syntax-private-property-in-object': 7.14.5(@babel/core@7.22.1)
    transitivePeerDependencies:
      - supports-color
    dev: false

  /@babel/plugin-transform-property-literals@7.18.6(@babel/core@7.22.1):
    resolution: {integrity: sha512-cYcs6qlgafTud3PAzrrRNbQtfpQ8+y/+M5tKmksS9+M1ckbH6kzY8MrexEM9mcA6JDsukE19iIRvAyYl463sMg==}
    engines: {node: '>=6.9.0'}
    peerDependencies:
      '@babel/core': ^7.0.0-0
    dependencies:
      '@babel/core': 7.22.1
      '@babel/helper-plugin-utils': 7.21.5
    dev: false

  /@babel/plugin-transform-react-constant-elements@7.22.3(@babel/core@7.22.1):
    resolution: {integrity: sha512-b5J6muxQYp4H7loAQv/c7GO5cPuRA6H5hx4gO+/Hn+Cu9MRQU0PNiUoWq1L//8sq6kFSNxGXFb2XTaUfa9y+Pg==}
    engines: {node: '>=6.9.0'}
    peerDependencies:
      '@babel/core': ^7.0.0-0
    dependencies:
      '@babel/core': 7.22.1
      '@babel/helper-plugin-utils': 7.21.5
    dev: false

  /@babel/plugin-transform-react-display-name@7.18.6(@babel/core@7.22.1):
    resolution: {integrity: sha512-TV4sQ+T013n61uMoygyMRm+xf04Bd5oqFpv2jAEQwSZ8NwQA7zeRPg1LMVg2PWi3zWBz+CLKD+v5bcpZ/BS0aA==}
    engines: {node: '>=6.9.0'}
    peerDependencies:
      '@babel/core': ^7.0.0-0
    dependencies:
      '@babel/core': 7.22.1
      '@babel/helper-plugin-utils': 7.21.5
    dev: false

  /@babel/plugin-transform-react-jsx-development@7.18.6(@babel/core@7.22.1):
    resolution: {integrity: sha512-SA6HEjwYFKF7WDjWcMcMGUimmw/nhNRDWxr+KaLSCrkD/LMDBvWRmHAYgE1HDeF8KUuI8OAu+RT6EOtKxSW2qA==}
    engines: {node: '>=6.9.0'}
    peerDependencies:
      '@babel/core': ^7.0.0-0
    dependencies:
      '@babel/core': 7.22.1
      '@babel/plugin-transform-react-jsx': 7.22.3(@babel/core@7.22.1)
    dev: false

  /@babel/plugin-transform-react-jsx@7.22.3(@babel/core@7.22.1):
    resolution: {integrity: sha512-JEulRWG2f04a7L8VWaOngWiK6p+JOSpB+DAtwfJgOaej1qdbNxqtK7MwTBHjUA10NeFcszlFNqCdbRcirzh2uQ==}
    engines: {node: '>=6.9.0'}
    peerDependencies:
      '@babel/core': ^7.0.0-0
    dependencies:
      '@babel/core': 7.22.1
      '@babel/helper-annotate-as-pure': 7.18.6
      '@babel/helper-module-imports': 7.21.4
      '@babel/helper-plugin-utils': 7.21.5
      '@babel/plugin-syntax-jsx': 7.21.4(@babel/core@7.22.1)
      '@babel/types': 7.22.4
    dev: false

  /@babel/plugin-transform-react-pure-annotations@7.18.6(@babel/core@7.22.1):
    resolution: {integrity: sha512-I8VfEPg9r2TRDdvnHgPepTKvuRomzA8+u+nhY7qSI1fR2hRNebasZEETLyM5mAUr0Ku56OkXJ0I7NHJnO6cJiQ==}
    engines: {node: '>=6.9.0'}
    peerDependencies:
      '@babel/core': ^7.0.0-0
    dependencies:
      '@babel/core': 7.22.1
      '@babel/helper-annotate-as-pure': 7.18.6
      '@babel/helper-plugin-utils': 7.21.5
    dev: false

  /@babel/plugin-transform-regenerator@7.21.5(@babel/core@7.22.1):
    resolution: {integrity: sha512-ZoYBKDb6LyMi5yCsByQ5jmXsHAQDDYeexT1Szvlmui+lADvfSecr5Dxd/PkrTC3pAD182Fcju1VQkB4oCp9M+w==}
    engines: {node: '>=6.9.0'}
    peerDependencies:
      '@babel/core': ^7.0.0-0
    dependencies:
      '@babel/core': 7.22.1
      '@babel/helper-plugin-utils': 7.21.5
      regenerator-transform: 0.15.1
    dev: false

  /@babel/plugin-transform-reserved-words@7.18.6(@babel/core@7.22.1):
    resolution: {integrity: sha512-oX/4MyMoypzHjFrT1CdivfKZ+XvIPMFXwwxHp/r0Ddy2Vuomt4HDFGmft1TAY2yiTKiNSsh3kjBAzcM8kSdsjA==}
    engines: {node: '>=6.9.0'}
    peerDependencies:
      '@babel/core': ^7.0.0-0
    dependencies:
      '@babel/core': 7.22.1
      '@babel/helper-plugin-utils': 7.21.5
    dev: false

  /@babel/plugin-transform-runtime@7.22.4(@babel/core@7.22.1):
    resolution: {integrity: sha512-Urkiz1m4zqiRo17klj+l3nXgiRTFQng91Bc1eiLF7BMQu1e7wE5Gcq9xSv062IF068NHjcutSbIMev60gXxAvA==}
    engines: {node: '>=6.9.0'}
    peerDependencies:
      '@babel/core': ^7.0.0-0
    dependencies:
      '@babel/core': 7.22.1
      '@babel/helper-module-imports': 7.21.4
      '@babel/helper-plugin-utils': 7.21.5
      babel-plugin-polyfill-corejs2: 0.4.3(@babel/core@7.22.1)
      babel-plugin-polyfill-corejs3: 0.8.1(@babel/core@7.22.1)
      babel-plugin-polyfill-regenerator: 0.5.0(@babel/core@7.22.1)
      semver: 6.3.0
    transitivePeerDependencies:
      - supports-color
    dev: false

  /@babel/plugin-transform-shorthand-properties@7.18.6(@babel/core@7.22.1):
    resolution: {integrity: sha512-eCLXXJqv8okzg86ywZJbRn19YJHU4XUa55oz2wbHhaQVn/MM+XhukiT7SYqp/7o00dg52Rj51Ny+Ecw4oyoygw==}
    engines: {node: '>=6.9.0'}
    peerDependencies:
      '@babel/core': ^7.0.0-0
    dependencies:
      '@babel/core': 7.22.1
      '@babel/helper-plugin-utils': 7.21.5
    dev: false

  /@babel/plugin-transform-spread@7.20.7(@babel/core@7.22.1):
    resolution: {integrity: sha512-ewBbHQ+1U/VnH1fxltbJqDeWBU1oNLG8Dj11uIv3xVf7nrQu0bPGe5Rf716r7K5Qz+SqtAOVswoVunoiBtGhxw==}
    engines: {node: '>=6.9.0'}
    peerDependencies:
      '@babel/core': ^7.0.0-0
    dependencies:
      '@babel/core': 7.22.1
      '@babel/helper-plugin-utils': 7.21.5
      '@babel/helper-skip-transparent-expression-wrappers': 7.20.0
    dev: false

  /@babel/plugin-transform-sticky-regex@7.18.6(@babel/core@7.22.1):
    resolution: {integrity: sha512-kfiDrDQ+PBsQDO85yj1icueWMfGfJFKN1KCkndygtu/C9+XUfydLC8Iv5UYJqRwy4zk8EcplRxEOeLyjq1gm6Q==}
    engines: {node: '>=6.9.0'}
    peerDependencies:
      '@babel/core': ^7.0.0-0
    dependencies:
      '@babel/core': 7.22.1
      '@babel/helper-plugin-utils': 7.21.5
    dev: false

  /@babel/plugin-transform-template-literals@7.18.9(@babel/core@7.22.1):
    resolution: {integrity: sha512-S8cOWfT82gTezpYOiVaGHrCbhlHgKhQt8XH5ES46P2XWmX92yisoZywf5km75wv5sYcXDUCLMmMxOLCtthDgMA==}
    engines: {node: '>=6.9.0'}
    peerDependencies:
      '@babel/core': ^7.0.0-0
    dependencies:
      '@babel/core': 7.22.1
      '@babel/helper-plugin-utils': 7.21.5
    dev: false

  /@babel/plugin-transform-typeof-symbol@7.18.9(@babel/core@7.22.1):
    resolution: {integrity: sha512-SRfwTtF11G2aemAZWivL7PD+C9z52v9EvMqH9BuYbabyPuKUvSWks3oCg6041pT925L4zVFqaVBeECwsmlguEw==}
    engines: {node: '>=6.9.0'}
    peerDependencies:
      '@babel/core': ^7.0.0-0
    dependencies:
      '@babel/core': 7.22.1
      '@babel/helper-plugin-utils': 7.21.5
    dev: false

  /@babel/plugin-transform-typescript@7.22.3(@babel/core@7.22.1):
    resolution: {integrity: sha512-pyjnCIniO5PNaEuGxT28h0HbMru3qCVrMqVgVOz/krComdIrY9W6FCLBq9NWHY8HDGaUlan+UhmZElDENIfCcw==}
    engines: {node: '>=6.9.0'}
    peerDependencies:
      '@babel/core': ^7.0.0-0
    dependencies:
      '@babel/core': 7.22.1
      '@babel/helper-annotate-as-pure': 7.18.6
      '@babel/helper-create-class-features-plugin': 7.22.1(@babel/core@7.22.1)
      '@babel/helper-plugin-utils': 7.21.5
      '@babel/plugin-syntax-typescript': 7.21.4(@babel/core@7.22.1)
    transitivePeerDependencies:
      - supports-color
    dev: false

  /@babel/plugin-transform-unicode-escapes@7.21.5(@babel/core@7.22.1):
    resolution: {integrity: sha512-LYm/gTOwZqsYohlvFUe/8Tujz75LqqVC2w+2qPHLR+WyWHGCZPN1KBpJCJn+4Bk4gOkQy/IXKIge6az5MqwlOg==}
    engines: {node: '>=6.9.0'}
    peerDependencies:
      '@babel/core': ^7.0.0-0
    dependencies:
      '@babel/core': 7.22.1
      '@babel/helper-plugin-utils': 7.21.5
    dev: false

  /@babel/plugin-transform-unicode-property-regex@7.22.3(@babel/core@7.22.1):
    resolution: {integrity: sha512-5ScJ+OmdX+O6HRuMGW4kv7RL9vIKdtdAj9wuWUKy1wbHY3jaM/UlyIiC1G7J6UJiiyMukjjK0QwL3P0vBd0yYg==}
    engines: {node: '>=6.9.0'}
    peerDependencies:
      '@babel/core': ^7.0.0-0
    dependencies:
      '@babel/core': 7.22.1
      '@babel/helper-create-regexp-features-plugin': 7.22.1(@babel/core@7.22.1)
      '@babel/helper-plugin-utils': 7.21.5
    dev: false

  /@babel/plugin-transform-unicode-regex@7.18.6(@babel/core@7.22.1):
    resolution: {integrity: sha512-gE7A6Lt7YLnNOL3Pb9BNeZvi+d8l7tcRrG4+pwJjK9hD2xX4mEvjlQW60G9EEmfXVYRPv9VRQcyegIVHCql/AA==}
    engines: {node: '>=6.9.0'}
    peerDependencies:
      '@babel/core': ^7.0.0-0
    dependencies:
      '@babel/core': 7.22.1
      '@babel/helper-create-regexp-features-plugin': 7.22.1(@babel/core@7.22.1)
      '@babel/helper-plugin-utils': 7.21.5
    dev: false

  /@babel/plugin-transform-unicode-sets-regex@7.22.3(@babel/core@7.22.1):
    resolution: {integrity: sha512-hNufLdkF8vqywRp+P55j4FHXqAX2LRUccoZHH7AFn1pq5ZOO2ISKW9w13bFZVjBoTqeve2HOgoJCcaziJVhGNw==}
    engines: {node: '>=6.9.0'}
    peerDependencies:
      '@babel/core': ^7.0.0
    dependencies:
      '@babel/core': 7.22.1
      '@babel/helper-create-regexp-features-plugin': 7.22.1(@babel/core@7.22.1)
      '@babel/helper-plugin-utils': 7.21.5
    dev: false

  /@babel/preset-env@7.22.4(@babel/core@7.22.1):
    resolution: {integrity: sha512-c3lHOjbwBv0TkhYCr+XCR6wKcSZ1QbQTVdSkZUaVpLv8CVWotBMArWUi5UAJrcrQaEnleVkkvaV8F/pmc/STZQ==}
    engines: {node: '>=6.9.0'}
    peerDependencies:
      '@babel/core': ^7.0.0-0
    dependencies:
      '@babel/compat-data': 7.22.3
      '@babel/core': 7.22.1
      '@babel/helper-compilation-targets': 7.22.1(@babel/core@7.22.1)
      '@babel/helper-plugin-utils': 7.21.5
      '@babel/helper-validator-option': 7.21.0
      '@babel/plugin-bugfix-safari-id-destructuring-collision-in-function-expression': 7.18.6(@babel/core@7.22.1)
      '@babel/plugin-bugfix-v8-spread-parameters-in-optional-chaining': 7.22.3(@babel/core@7.22.1)
      '@babel/plugin-proposal-private-property-in-object': 7.21.11(@babel/core@7.22.1)
      '@babel/plugin-syntax-async-generators': 7.8.4(@babel/core@7.22.1)
      '@babel/plugin-syntax-class-properties': 7.12.13(@babel/core@7.22.1)
      '@babel/plugin-syntax-class-static-block': 7.14.5(@babel/core@7.22.1)
      '@babel/plugin-syntax-dynamic-import': 7.8.3(@babel/core@7.22.1)
      '@babel/plugin-syntax-export-namespace-from': 7.8.3(@babel/core@7.22.1)
      '@babel/plugin-syntax-import-assertions': 7.20.0(@babel/core@7.22.1)
      '@babel/plugin-syntax-import-attributes': 7.22.3(@babel/core@7.22.1)
      '@babel/plugin-syntax-import-meta': 7.10.4(@babel/core@7.22.1)
      '@babel/plugin-syntax-json-strings': 7.8.3(@babel/core@7.22.1)
      '@babel/plugin-syntax-logical-assignment-operators': 7.10.4(@babel/core@7.22.1)
      '@babel/plugin-syntax-nullish-coalescing-operator': 7.8.3(@babel/core@7.22.1)
      '@babel/plugin-syntax-numeric-separator': 7.10.4(@babel/core@7.22.1)
      '@babel/plugin-syntax-object-rest-spread': 7.8.3(@babel/core@7.22.1)
      '@babel/plugin-syntax-optional-catch-binding': 7.8.3(@babel/core@7.22.1)
      '@babel/plugin-syntax-optional-chaining': 7.8.3(@babel/core@7.22.1)
      '@babel/plugin-syntax-private-property-in-object': 7.14.5(@babel/core@7.22.1)
      '@babel/plugin-syntax-top-level-await': 7.14.5(@babel/core@7.22.1)
      '@babel/plugin-syntax-unicode-sets-regex': 7.18.6(@babel/core@7.22.1)
      '@babel/plugin-transform-arrow-functions': 7.21.5(@babel/core@7.22.1)
      '@babel/plugin-transform-async-generator-functions': 7.22.3(@babel/core@7.22.1)
      '@babel/plugin-transform-async-to-generator': 7.20.7(@babel/core@7.22.1)
      '@babel/plugin-transform-block-scoped-functions': 7.18.6(@babel/core@7.22.1)
      '@babel/plugin-transform-block-scoping': 7.21.0(@babel/core@7.22.1)
      '@babel/plugin-transform-class-properties': 7.22.3(@babel/core@7.22.1)
      '@babel/plugin-transform-class-static-block': 7.22.3(@babel/core@7.22.1)
      '@babel/plugin-transform-classes': 7.21.0(@babel/core@7.22.1)
      '@babel/plugin-transform-computed-properties': 7.21.5(@babel/core@7.22.1)
      '@babel/plugin-transform-destructuring': 7.21.3(@babel/core@7.22.1)
      '@babel/plugin-transform-dotall-regex': 7.18.6(@babel/core@7.22.1)
      '@babel/plugin-transform-duplicate-keys': 7.18.9(@babel/core@7.22.1)
      '@babel/plugin-transform-dynamic-import': 7.22.1(@babel/core@7.22.1)
      '@babel/plugin-transform-exponentiation-operator': 7.18.6(@babel/core@7.22.1)
      '@babel/plugin-transform-export-namespace-from': 7.22.3(@babel/core@7.22.1)
      '@babel/plugin-transform-for-of': 7.21.5(@babel/core@7.22.1)
      '@babel/plugin-transform-function-name': 7.18.9(@babel/core@7.22.1)
      '@babel/plugin-transform-json-strings': 7.22.3(@babel/core@7.22.1)
      '@babel/plugin-transform-literals': 7.18.9(@babel/core@7.22.1)
      '@babel/plugin-transform-logical-assignment-operators': 7.22.3(@babel/core@7.22.1)
      '@babel/plugin-transform-member-expression-literals': 7.18.6(@babel/core@7.22.1)
      '@babel/plugin-transform-modules-amd': 7.20.11(@babel/core@7.22.1)
      '@babel/plugin-transform-modules-commonjs': 7.21.5(@babel/core@7.22.1)
      '@babel/plugin-transform-modules-systemjs': 7.22.3(@babel/core@7.22.1)
      '@babel/plugin-transform-modules-umd': 7.18.6(@babel/core@7.22.1)
      '@babel/plugin-transform-named-capturing-groups-regex': 7.22.3(@babel/core@7.22.1)
      '@babel/plugin-transform-new-target': 7.22.3(@babel/core@7.22.1)
      '@babel/plugin-transform-nullish-coalescing-operator': 7.22.3(@babel/core@7.22.1)
      '@babel/plugin-transform-numeric-separator': 7.22.3(@babel/core@7.22.1)
      '@babel/plugin-transform-object-rest-spread': 7.22.3(@babel/core@7.22.1)
      '@babel/plugin-transform-object-super': 7.18.6(@babel/core@7.22.1)
      '@babel/plugin-transform-optional-catch-binding': 7.22.3(@babel/core@7.22.1)
      '@babel/plugin-transform-optional-chaining': 7.22.3(@babel/core@7.22.1)
      '@babel/plugin-transform-parameters': 7.22.3(@babel/core@7.22.1)
      '@babel/plugin-transform-private-methods': 7.22.3(@babel/core@7.22.1)
      '@babel/plugin-transform-private-property-in-object': 7.22.3(@babel/core@7.22.1)
      '@babel/plugin-transform-property-literals': 7.18.6(@babel/core@7.22.1)
      '@babel/plugin-transform-regenerator': 7.21.5(@babel/core@7.22.1)
      '@babel/plugin-transform-reserved-words': 7.18.6(@babel/core@7.22.1)
      '@babel/plugin-transform-shorthand-properties': 7.18.6(@babel/core@7.22.1)
      '@babel/plugin-transform-spread': 7.20.7(@babel/core@7.22.1)
      '@babel/plugin-transform-sticky-regex': 7.18.6(@babel/core@7.22.1)
      '@babel/plugin-transform-template-literals': 7.18.9(@babel/core@7.22.1)
      '@babel/plugin-transform-typeof-symbol': 7.18.9(@babel/core@7.22.1)
      '@babel/plugin-transform-unicode-escapes': 7.21.5(@babel/core@7.22.1)
      '@babel/plugin-transform-unicode-property-regex': 7.22.3(@babel/core@7.22.1)
      '@babel/plugin-transform-unicode-regex': 7.18.6(@babel/core@7.22.1)
      '@babel/plugin-transform-unicode-sets-regex': 7.22.3(@babel/core@7.22.1)
      '@babel/preset-modules': 0.1.5(@babel/core@7.22.1)
      '@babel/types': 7.22.4
      babel-plugin-polyfill-corejs2: 0.4.3(@babel/core@7.22.1)
      babel-plugin-polyfill-corejs3: 0.8.1(@babel/core@7.22.1)
      babel-plugin-polyfill-regenerator: 0.5.0(@babel/core@7.22.1)
      core-js-compat: 3.30.2
      semver: 6.3.0
    transitivePeerDependencies:
      - supports-color
    dev: false

  /@babel/preset-modules@0.1.5(@babel/core@7.22.1):
    resolution: {integrity: sha512-A57th6YRG7oR3cq/yt/Y84MvGgE0eJG2F1JLhKuyG+jFxEgrd/HAMJatiFtmOiZurz+0DkrvbheCLaV5f2JfjA==}
    peerDependencies:
      '@babel/core': ^7.0.0-0
    dependencies:
      '@babel/core': 7.22.1
      '@babel/helper-plugin-utils': 7.21.5
      '@babel/plugin-proposal-unicode-property-regex': 7.18.6(@babel/core@7.22.1)
      '@babel/plugin-transform-dotall-regex': 7.18.6(@babel/core@7.22.1)
      '@babel/types': 7.22.4
      esutils: 2.0.3
    dev: false

  /@babel/preset-react@7.22.3(@babel/core@7.22.1):
    resolution: {integrity: sha512-lxDz1mnZ9polqClBCVBjIVUypoB4qV3/tZUDb/IlYbW1kiiLaXaX+bInbRjl+lNQ/iUZraQ3+S8daEmoELMWug==}
    engines: {node: '>=6.9.0'}
    peerDependencies:
      '@babel/core': ^7.0.0-0
    dependencies:
      '@babel/core': 7.22.1
      '@babel/helper-plugin-utils': 7.21.5
      '@babel/helper-validator-option': 7.21.0
      '@babel/plugin-transform-react-display-name': 7.18.6(@babel/core@7.22.1)
      '@babel/plugin-transform-react-jsx': 7.22.3(@babel/core@7.22.1)
      '@babel/plugin-transform-react-jsx-development': 7.18.6(@babel/core@7.22.1)
      '@babel/plugin-transform-react-pure-annotations': 7.18.6(@babel/core@7.22.1)
    dev: false

  /@babel/preset-typescript@7.21.5(@babel/core@7.22.1):
    resolution: {integrity: sha512-iqe3sETat5EOrORXiQ6rWfoOg2y68Cs75B9wNxdPW4kixJxh7aXQE1KPdWLDniC24T/6dSnguF33W9j/ZZQcmA==}
    engines: {node: '>=6.9.0'}
    peerDependencies:
      '@babel/core': ^7.0.0-0
    dependencies:
      '@babel/core': 7.22.1
      '@babel/helper-plugin-utils': 7.21.5
      '@babel/helper-validator-option': 7.21.0
      '@babel/plugin-syntax-jsx': 7.21.4(@babel/core@7.22.1)
      '@babel/plugin-transform-modules-commonjs': 7.21.5(@babel/core@7.22.1)
      '@babel/plugin-transform-typescript': 7.22.3(@babel/core@7.22.1)
    transitivePeerDependencies:
      - supports-color
    dev: false

  /@babel/regjsgen@0.8.0:
    resolution: {integrity: sha512-x/rqGMdzj+fWZvCOYForTghzbtqPDZ5gPwaoNGHdgDfF2QA/XZbCBp4Moo5scrkAMPhB7z26XM/AaHuIJdgauA==}
    dev: false

  /@babel/runtime@7.22.3:
    resolution: {integrity: sha512-XsDuspWKLUsxwCp6r7EhsExHtYfbe5oAGQ19kqngTdCPUoPQzOPdUbD/pB9PJiwb2ptYKQDjSJT3R6dC+EPqfQ==}
    engines: {node: '>=6.9.0'}
    dependencies:
      regenerator-runtime: 0.13.11
    dev: false

  /@babel/template@7.21.9:
    resolution: {integrity: sha512-MK0X5k8NKOuWRamiEfc3KEJiHMTkGZNUjzMipqCGDDc6ijRl/B7RGSKVGncu4Ro/HdyzzY6cmoXuKI2Gffk7vQ==}
    engines: {node: '>=6.9.0'}
    dependencies:
      '@babel/code-frame': 7.21.4
      '@babel/parser': 7.22.4
      '@babel/types': 7.22.4
    dev: false

  /@babel/traverse@7.22.4:
    resolution: {integrity: sha512-Tn1pDsjIcI+JcLKq1AVlZEr4226gpuAQTsLMorsYg9tuS/kG7nuwwJ4AB8jfQuEgb/COBwR/DqJxmoiYFu5/rQ==}
    engines: {node: '>=6.9.0'}
    dependencies:
      '@babel/code-frame': 7.21.4
      '@babel/generator': 7.22.3
      '@babel/helper-environment-visitor': 7.22.1
      '@babel/helper-function-name': 7.21.0
      '@babel/helper-hoist-variables': 7.18.6
      '@babel/helper-split-export-declaration': 7.18.6
      '@babel/parser': 7.22.4
      '@babel/types': 7.22.4
      debug: 4.3.4
      globals: 11.12.0
    transitivePeerDependencies:
      - supports-color
    dev: false

  /@babel/types@7.22.4:
    resolution: {integrity: sha512-Tx9x3UBHTTsMSW85WB2kphxYQVvrZ/t1FxD88IpSgIjiUJlCm9z+xWIDwyo1vffTwSqteqyznB8ZE9vYYk16zA==}
    engines: {node: '>=6.9.0'}
    dependencies:
      '@babel/helper-string-parser': 7.21.5
      '@babel/helper-validator-identifier': 7.19.1
      to-fast-properties: 2.0.0
    dev: false

  /@bcoe/v8-coverage@0.2.3:
    resolution: {integrity: sha512-0hYQ8SB4Db5zvZB4axdMHGwEaQjkZzFjQiN9LVYvIFB2nSUHW9tYpxWriPrWDASIxiaXax83REcLxuSdnGPZtw==}
    dev: false

  /@csstools/normalize.css@12.0.0:
    resolution: {integrity: sha512-M0qqxAcwCsIVfpFQSlGN5XjXWu8l5JDZN+fPt1LeW5SZexQTgnaEvgXAY+CeygRw0EeppWHi12JxESWiWrB0Sg==}
    dev: false

  /@csstools/postcss-cascade-layers@1.1.1(postcss@8.4.24):
    resolution: {integrity: sha512-+KdYrpKC5TgomQr2DlZF4lDEpHcoxnj5IGddYYfBWJAKfj1JtuHUIqMa+E1pJJ+z3kvDViWMqyqPlG4Ja7amQA==}
    engines: {node: ^12 || ^14 || >=16}
    peerDependencies:
      postcss: ^8.2
    dependencies:
      '@csstools/selector-specificity': 2.2.0(postcss-selector-parser@6.0.13)
      postcss: 8.4.24
      postcss-selector-parser: 6.0.13
    dev: false

  /@csstools/postcss-color-function@1.1.1(postcss@8.4.24):
    resolution: {integrity: sha512-Bc0f62WmHdtRDjf5f3e2STwRAl89N2CLb+9iAwzrv4L2hncrbDwnQD9PCq0gtAt7pOI2leIV08HIBUd4jxD8cw==}
    engines: {node: ^12 || ^14 || >=16}
    peerDependencies:
      postcss: ^8.2
    dependencies:
      '@csstools/postcss-progressive-custom-properties': 1.3.0(postcss@8.4.24)
      postcss: 8.4.24
      postcss-value-parser: 4.2.0
    dev: false

  /@csstools/postcss-font-format-keywords@1.0.1(postcss@8.4.24):
    resolution: {integrity: sha512-ZgrlzuUAjXIOc2JueK0X5sZDjCtgimVp/O5CEqTcs5ShWBa6smhWYbS0x5cVc/+rycTDbjjzoP0KTDnUneZGOg==}
    engines: {node: ^12 || ^14 || >=16}
    peerDependencies:
      postcss: ^8.2
    dependencies:
      postcss: 8.4.24
      postcss-value-parser: 4.2.0
    dev: false

  /@csstools/postcss-hwb-function@1.0.2(postcss@8.4.24):
    resolution: {integrity: sha512-YHdEru4o3Rsbjmu6vHy4UKOXZD+Rn2zmkAmLRfPet6+Jz4Ojw8cbWxe1n42VaXQhD3CQUXXTooIy8OkVbUcL+w==}
    engines: {node: ^12 || ^14 || >=16}
    peerDependencies:
      postcss: ^8.2
    dependencies:
      postcss: 8.4.24
      postcss-value-parser: 4.2.0
    dev: false

  /@csstools/postcss-ic-unit@1.0.1(postcss@8.4.24):
    resolution: {integrity: sha512-Ot1rcwRAaRHNKC9tAqoqNZhjdYBzKk1POgWfhN4uCOE47ebGcLRqXjKkApVDpjifL6u2/55ekkpnFcp+s/OZUw==}
    engines: {node: ^12 || ^14 || >=16}
    peerDependencies:
      postcss: ^8.2
    dependencies:
      '@csstools/postcss-progressive-custom-properties': 1.3.0(postcss@8.4.24)
      postcss: 8.4.24
      postcss-value-parser: 4.2.0
    dev: false

  /@csstools/postcss-is-pseudo-class@2.0.7(postcss@8.4.24):
    resolution: {integrity: sha512-7JPeVVZHd+jxYdULl87lvjgvWldYu+Bc62s9vD/ED6/QTGjy0jy0US/f6BG53sVMTBJ1lzKZFpYmofBN9eaRiA==}
    engines: {node: ^12 || ^14 || >=16}
    peerDependencies:
      postcss: ^8.2
    dependencies:
      '@csstools/selector-specificity': 2.2.0(postcss-selector-parser@6.0.13)
      postcss: 8.4.24
      postcss-selector-parser: 6.0.13
    dev: false

  /@csstools/postcss-nested-calc@1.0.0(postcss@8.4.24):
    resolution: {integrity: sha512-JCsQsw1wjYwv1bJmgjKSoZNvf7R6+wuHDAbi5f/7MbFhl2d/+v+TvBTU4BJH3G1X1H87dHl0mh6TfYogbT/dJQ==}
    engines: {node: ^12 || ^14 || >=16}
    peerDependencies:
      postcss: ^8.2
    dependencies:
      postcss: 8.4.24
      postcss-value-parser: 4.2.0
    dev: false

  /@csstools/postcss-normalize-display-values@1.0.1(postcss@8.4.24):
    resolution: {integrity: sha512-jcOanIbv55OFKQ3sYeFD/T0Ti7AMXc9nM1hZWu8m/2722gOTxFg7xYu4RDLJLeZmPUVQlGzo4jhzvTUq3x4ZUw==}
    engines: {node: ^12 || ^14 || >=16}
    peerDependencies:
      postcss: ^8.2
    dependencies:
      postcss: 8.4.24
      postcss-value-parser: 4.2.0
    dev: false

  /@csstools/postcss-oklab-function@1.1.1(postcss@8.4.24):
    resolution: {integrity: sha512-nJpJgsdA3dA9y5pgyb/UfEzE7W5Ka7u0CX0/HIMVBNWzWemdcTH3XwANECU6anWv/ao4vVNLTMxhiPNZsTK6iA==}
    engines: {node: ^12 || ^14 || >=16}
    peerDependencies:
      postcss: ^8.2
    dependencies:
      '@csstools/postcss-progressive-custom-properties': 1.3.0(postcss@8.4.24)
      postcss: 8.4.24
      postcss-value-parser: 4.2.0
    dev: false

  /@csstools/postcss-progressive-custom-properties@1.3.0(postcss@8.4.24):
    resolution: {integrity: sha512-ASA9W1aIy5ygskZYuWams4BzafD12ULvSypmaLJT2jvQ8G0M3I8PRQhC0h7mG0Z3LI05+agZjqSR9+K9yaQQjA==}
    engines: {node: ^12 || ^14 || >=16}
    peerDependencies:
      postcss: ^8.3
    dependencies:
      postcss: 8.4.24
      postcss-value-parser: 4.2.0
    dev: false

  /@csstools/postcss-stepped-value-functions@1.0.1(postcss@8.4.24):
    resolution: {integrity: sha512-dz0LNoo3ijpTOQqEJLY8nyaapl6umbmDcgj4AD0lgVQ572b2eqA1iGZYTTWhrcrHztWDDRAX2DGYyw2VBjvCvQ==}
    engines: {node: ^12 || ^14 || >=16}
    peerDependencies:
      postcss: ^8.2
    dependencies:
      postcss: 8.4.24
      postcss-value-parser: 4.2.0
    dev: false

  /@csstools/postcss-text-decoration-shorthand@1.0.0(postcss@8.4.24):
    resolution: {integrity: sha512-c1XwKJ2eMIWrzQenN0XbcfzckOLLJiczqy+YvfGmzoVXd7pT9FfObiSEfzs84bpE/VqfpEuAZ9tCRbZkZxxbdw==}
    engines: {node: ^12 || ^14 || >=16}
    peerDependencies:
      postcss: ^8.2
    dependencies:
      postcss: 8.4.24
      postcss-value-parser: 4.2.0
    dev: false

  /@csstools/postcss-trigonometric-functions@1.0.2(postcss@8.4.24):
    resolution: {integrity: sha512-woKaLO///4bb+zZC2s80l+7cm07M7268MsyG3M0ActXXEFi6SuhvriQYcb58iiKGbjwwIU7n45iRLEHypB47Og==}
    engines: {node: ^14 || >=16}
    peerDependencies:
      postcss: ^8.2
    dependencies:
      postcss: 8.4.24
      postcss-value-parser: 4.2.0
    dev: false

  /@csstools/postcss-unset-value@1.0.2(postcss@8.4.24):
    resolution: {integrity: sha512-c8J4roPBILnelAsdLr4XOAR/GsTm0GJi4XpcfvoWk3U6KiTCqiFYc63KhRMQQX35jYMp4Ao8Ij9+IZRgMfJp1g==}
    engines: {node: ^12 || ^14 || >=16}
    peerDependencies:
      postcss: ^8.2
    dependencies:
      postcss: 8.4.24
    dev: false

  /@csstools/selector-specificity@2.2.0(postcss-selector-parser@6.0.13):
    resolution: {integrity: sha512-+OJ9konv95ClSTOJCmMZqpd5+YGsB2S+x6w3E1oaM8UuR5j8nTNHYSz8c9BEPGDOCMQYIEEGlVPj/VY64iTbGw==}
    engines: {node: ^14 || ^16 || >=18}
    peerDependencies:
      postcss-selector-parser: ^6.0.10
    dependencies:
      postcss-selector-parser: 6.0.13
    dev: false

  /@emotion/babel-plugin@11.11.0:
    resolution: {integrity: sha512-m4HEDZleaaCH+XgDDsPF15Ht6wTLsgDTeR3WYj9Q/k76JtWhrJjcP4+/XlG8LGT/Rol9qUfOIztXeA84ATpqPQ==}
    dependencies:
      '@babel/helper-module-imports': 7.21.4
      '@babel/runtime': 7.22.3
      '@emotion/hash': 0.9.1
      '@emotion/memoize': 0.8.1
      '@emotion/serialize': 1.1.2
      babel-plugin-macros: 3.1.0
      convert-source-map: 1.9.0
      escape-string-regexp: 4.0.0
      find-root: 1.1.0
      source-map: 0.5.7
      stylis: 4.2.0
    dev: false

  /@emotion/cache@11.11.0:
    resolution: {integrity: sha512-P34z9ssTCBi3e9EI1ZsWpNHcfY1r09ZO0rZbRO2ob3ZQMnFI35jB536qoXbkdesr5EUhYi22anuEJuyxifaqAQ==}
    dependencies:
      '@emotion/memoize': 0.8.1
      '@emotion/sheet': 1.2.2
      '@emotion/utils': 1.2.1
      '@emotion/weak-memoize': 0.3.1
      stylis: 4.2.0
    dev: false

  /@emotion/hash@0.9.1:
    resolution: {integrity: sha512-gJB6HLm5rYwSLI6PQa+X1t5CFGrv1J1TWG+sOyMCeKz2ojaj6Fnl/rZEspogG+cvqbt4AE/2eIyD2QfLKTBNlQ==}
    dev: false

  /@emotion/is-prop-valid@1.2.1:
    resolution: {integrity: sha512-61Mf7Ufx4aDxx1xlDeOm8aFFigGHE4z+0sKCa+IHCeZKiyP9RLD0Mmx7m8b9/Cf37f7NAvQOOJAbQQGVr5uERw==}
    dependencies:
      '@emotion/memoize': 0.8.1
    dev: false

  /@emotion/memoize@0.8.1:
    resolution: {integrity: sha512-W2P2c/VRW1/1tLox0mVUalvnWXxavmv/Oum2aPsRcoDJuob75FC3Y8FbpfLwUegRcxINtGUMPq0tFCvYNTBXNA==}
    dev: false

  /@emotion/react@11.7.1(@babel/core@7.22.1)(react@17.0.2):
    resolution: {integrity: sha512-DV2Xe3yhkF1yT4uAUoJcYL1AmrnO5SVsdfvu+fBuS7IbByDeTVx9+wFmvx9Idzv7/78+9Mgx2Hcmr7Fex3tIyw==}
    peerDependencies:
      '@babel/core': ^7.0.0
      '@types/react': '*'
      react: '>=16.8.0'
    peerDependenciesMeta:
      '@babel/core':
        optional: true
      '@types/react':
        optional: true
    dependencies:
      '@babel/core': 7.22.1
      '@babel/runtime': 7.22.3
      '@emotion/cache': 11.11.0
      '@emotion/serialize': 1.1.2
      '@emotion/sheet': 1.2.2
      '@emotion/utils': 1.2.1
      '@emotion/weak-memoize': 0.2.5
      hoist-non-react-statics: 3.3.2
      react: 17.0.2
    dev: false

  /@emotion/serialize@1.1.2:
    resolution: {integrity: sha512-zR6a/fkFP4EAcCMQtLOhIgpprZOwNmCldtpaISpvz348+DP4Mz8ZoKaGGCQpbzepNIUWbq4w6hNZkwDyKoS+HA==}
    dependencies:
      '@emotion/hash': 0.9.1
      '@emotion/memoize': 0.8.1
      '@emotion/unitless': 0.8.1
      '@emotion/utils': 1.2.1
      csstype: 3.1.2
    dev: false

  /@emotion/sheet@1.2.2:
    resolution: {integrity: sha512-0QBtGvaqtWi+nx6doRwDdBIzhNdZrXUppvTM4dtZZWEGTXL/XE/yJxLMGlDT1Gt+UHH5IX1n+jkXyytE/av7OA==}
    dev: false

  /@emotion/styled@11.6.0(@babel/core@7.22.1)(@emotion/react@11.7.1)(react@17.0.2):
    resolution: {integrity: sha512-mxVtVyIOTmCAkFbwIp+nCjTXJNgcz4VWkOYQro87jE2QBTydnkiYusMrRGFtzuruiGK4dDaNORk4gH049iiQuw==}
    peerDependencies:
      '@babel/core': ^7.0.0
      '@emotion/react': ^11.0.0-rc.0
      '@types/react': '*'
      react: '>=16.8.0'
    peerDependenciesMeta:
      '@babel/core':
        optional: true
      '@types/react':
        optional: true
    dependencies:
      '@babel/core': 7.22.1
      '@babel/runtime': 7.22.3
      '@emotion/babel-plugin': 11.11.0
      '@emotion/is-prop-valid': 1.2.1
      '@emotion/react': 11.7.1(@babel/core@7.22.1)(react@17.0.2)
      '@emotion/serialize': 1.1.2
      '@emotion/utils': 1.2.1
      react: 17.0.2
    dev: false

  /@emotion/unitless@0.8.1:
    resolution: {integrity: sha512-KOEGMu6dmJZtpadb476IsZBclKvILjopjUii3V+7MnXIQCYh8W3NgNcgwo21n9LXZX6EDIKvqfjYxXebDwxKmQ==}
    dev: false

  /@emotion/utils@1.2.1:
    resolution: {integrity: sha512-Y2tGf3I+XVnajdItskUCn6LX+VUDmP6lTL4fcqsXAv43dnlbZiuW4MWQW38rW/BVWSE7Q/7+XQocmpnRYILUmg==}
    dev: false

  /@emotion/weak-memoize@0.2.5:
    resolution: {integrity: sha512-6U71C2Wp7r5XtFtQzYrW5iKFT67OixrSxjI4MptCHzdSVlgabczzqLe0ZSgnub/5Kp4hSbpDB1tMytZY9pwxxA==}
    dev: false

  /@emotion/weak-memoize@0.3.1:
    resolution: {integrity: sha512-EsBwpc7hBUJWAsNPBmJy4hxWx12v6bshQsldrVmjxJoc3isbxhOrF2IcCpaXxfvq03NwkI7sbsOLXbYuqF/8Ww==}
    dev: false

  /@eslint-community/eslint-utils@4.4.0(eslint@8.42.0):
    resolution: {integrity: sha512-1/sA4dwrzBAyeUoQ6oxahHKmrZvsnLCg4RfxW3ZFGGmQkSNQPFNLV9CUEFQP1x9EYXHTo5p6xdhZM1Ne9p/AfA==}
    engines: {node: ^12.22.0 || ^14.17.0 || >=16.0.0}
    peerDependencies:
      eslint: ^6.0.0 || ^7.0.0 || >=8.0.0
    dependencies:
      eslint: 8.42.0
      eslint-visitor-keys: 3.4.1
    dev: false

  /@eslint-community/regexpp@4.5.1:
    resolution: {integrity: sha512-Z5ba73P98O1KUYCCJTUeVpja9RcGoMdncZ6T49FCUl2lN38JtCJ+3WgIDBv0AuY4WChU5PmtJmOCTlN6FZTFKQ==}
    engines: {node: ^12.0.0 || ^14.0.0 || >=16.0.0}
    dev: false

  /@eslint/eslintrc@2.0.3:
    resolution: {integrity: sha512-+5gy6OQfk+xx3q0d6jGZZC3f3KzAkXc/IanVxd1is/VIIziRqqt3ongQz0FiTUXqTk0c7aDB3OaFuKnuSoJicQ==}
    engines: {node: ^12.22.0 || ^14.17.0 || >=16.0.0}
    dependencies:
      ajv: 6.12.6
      debug: 4.3.4
      espree: 9.5.2
      globals: 13.20.0
      ignore: 5.2.4
      import-fresh: 3.3.0
      js-yaml: 4.1.0
      minimatch: 3.1.2
      strip-json-comments: 3.1.1
    transitivePeerDependencies:
      - supports-color
    dev: false

  /@eslint/js@8.42.0:
    resolution: {integrity: sha512-6SWlXpWU5AvId8Ac7zjzmIOqMOba/JWY8XZ4A7q7Gn1Vlfg/SFFIlrtHXt9nPn4op9ZPAkl91Jao+QQv3r/ukw==}
    engines: {node: ^12.22.0 || ^14.17.0 || >=16.0.0}
    dev: false

  /@fseehawer/react-circular-slider@2.6.1(global@4.4.0)(react-dom@17.0.2)(react@17.0.2):
    resolution: {integrity: sha512-98aIWV6VGi+CvCv26qG4uvfAOLuuu3T5sEJZrIUnpNw9oSIGadJ6GL7x3l7lYUgIYwsh26mmPW5K063hyrZFwg==}
    peerDependencies:
      global: ^4.4.0
      react: ^16.0.0 || ^17.0.0 || ^18.0.0
      react-dom: ^16.0.0 || ^17.0.0 || ^18.0.0
    dependencies:
      global: 4.4.0
      react: 17.0.2
      react-dom: 17.0.2(react@17.0.2)
    dev: false

  /@headlessui/react@1.7.15(react-dom@17.0.2)(react@17.0.2):
    resolution: {integrity: sha512-OTO0XtoRQ6JPB1cKNFYBZv2Q0JMqMGNhYP1CjPvcJvjz8YGokz8oAj89HIYZGN0gZzn/4kk9iUpmMF4Q21Gsqw==}
    engines: {node: '>=10'}
    peerDependencies:
      react: ^16 || ^17 || ^18
      react-dom: ^16 || ^17 || ^18
    dependencies:
      client-only: 0.0.1
      react: 17.0.2
      react-dom: 17.0.2(react@17.0.2)
    dev: false

  /@heroicons/react@2.0.18(react@17.0.2):
    resolution: {integrity: sha512-7TyMjRrZZMBPa+/5Y8lN0iyvUU/01PeMGX2+RE7cQWpEUIcb4QotzUObFkJDejj/HUH4qjP/eQ0gzzKs2f+6Yw==}
    peerDependencies:
      react: '>= 16'
    dependencies:
      react: 17.0.2
    dev: false

  /@humanwhocodes/config-array@0.11.10:
    resolution: {integrity: sha512-KVVjQmNUepDVGXNuoRRdmmEjruj0KfiGSbS8LVc12LMsWDQzRXJ0qdhN8L8uUigKpfEHRhlaQFY0ib1tnUbNeQ==}
    engines: {node: '>=10.10.0'}
    dependencies:
      '@humanwhocodes/object-schema': 1.2.1
      debug: 4.3.4
      minimatch: 3.1.2
    transitivePeerDependencies:
      - supports-color
    dev: false

  /@humanwhocodes/module-importer@1.0.1:
    resolution: {integrity: sha512-bxveV4V8v5Yb4ncFTT3rPSgZBOpCkjfK0y4oVVVJwIuDVBRMDXrPyXRL988i5ap9m9bnyEEjWfm5WkBmtffLfA==}
    engines: {node: '>=12.22'}
    dev: false

  /@humanwhocodes/object-schema@1.2.1:
    resolution: {integrity: sha512-ZnQMnLV4e7hDlUvw8H+U8ASL02SS2Gn6+9Ac3wGGLIe7+je2AeAOxPY+izIPJDfFDb7eDjev0Us8MO1iFRN8hA==}
    dev: false

  /@istanbuljs/load-nyc-config@1.1.0:
    resolution: {integrity: sha512-VjeHSlIzpv/NyD3N0YuHfXOPDIixcA1q2ZV98wsMqcYlPmv2n3Yb2lYP9XMElnaFVXg5A7YLTeLu6V84uQDjmQ==}
    engines: {node: '>=8'}
    dependencies:
      camelcase: 5.3.1
      find-up: 4.1.0
      get-package-type: 0.1.0
      js-yaml: 3.14.1
      resolve-from: 5.0.0
    dev: false

  /@istanbuljs/schema@0.1.3:
    resolution: {integrity: sha512-ZXRY4jNvVgSVQ8DL3LTcakaAtXwTVUxE81hslsyD2AtoXW/wVob10HkOJ1X/pAlcI7D+2YoZKg5do8G/w6RYgA==}
    engines: {node: '>=8'}
    dev: false

  /@jest/console@27.5.1:
    resolution: {integrity: sha512-kZ/tNpS3NXn0mlXXXPNuDZnb4c0oZ20r4K5eemM2k30ZC3G0T02nXUvyhf5YdbXWHPEJLc9qGLxEZ216MdL+Zg==}
    engines: {node: ^10.13.0 || ^12.13.0 || ^14.15.0 || >=15.0.0}
    dependencies:
      '@jest/types': 27.5.1
      '@types/node': 20.2.5
      chalk: 4.1.2
      jest-message-util: 27.5.1
      jest-util: 27.5.1
      slash: 3.0.0
    dev: false

  /@jest/console@28.1.3:
    resolution: {integrity: sha512-QPAkP5EwKdK/bxIr6C1I4Vs0rm2nHiANzj/Z5X2JQkrZo6IqvC4ldZ9K95tF0HdidhA8Bo6egxSzUFPYKcEXLw==}
    engines: {node: ^12.13.0 || ^14.15.0 || ^16.10.0 || >=17.0.0}
    dependencies:
      '@jest/types': 28.1.3
      '@types/node': 20.2.5
      chalk: 4.1.2
      jest-message-util: 28.1.3
      jest-util: 28.1.3
      slash: 3.0.0
    dev: false

  /@jest/core@27.5.1:
    resolution: {integrity: sha512-AK6/UTrvQD0Cd24NSqmIA6rKsu0tKIxfiCducZvqxYdmMisOYAsdItspT+fQDQYARPf8XgjAFZi0ogW2agH5nQ==}
    engines: {node: ^10.13.0 || ^12.13.0 || ^14.15.0 || >=15.0.0}
    peerDependencies:
      node-notifier: ^8.0.1 || ^9.0.0 || ^10.0.0
    peerDependenciesMeta:
      node-notifier:
        optional: true
    dependencies:
      '@jest/console': 27.5.1
      '@jest/reporters': 27.5.1
      '@jest/test-result': 27.5.1
      '@jest/transform': 27.5.1
      '@jest/types': 27.5.1
      '@types/node': 20.2.5
      ansi-escapes: 4.3.2
      chalk: 4.1.2
      emittery: 0.8.1
      exit: 0.1.2
      graceful-fs: 4.2.11
      jest-changed-files: 27.5.1
      jest-config: 27.5.1
      jest-haste-map: 27.5.1
      jest-message-util: 27.5.1
      jest-regex-util: 27.5.1
      jest-resolve: 27.5.1
      jest-resolve-dependencies: 27.5.1
      jest-runner: 27.5.1
      jest-runtime: 27.5.1
      jest-snapshot: 27.5.1
      jest-util: 27.5.1
      jest-validate: 27.5.1
      jest-watcher: 27.5.1
      micromatch: 4.0.5
      rimraf: 3.0.2
      slash: 3.0.0
      strip-ansi: 6.0.1
    transitivePeerDependencies:
      - bufferutil
      - canvas
      - supports-color
      - ts-node
      - utf-8-validate
    dev: false

  /@jest/environment@27.5.1:
    resolution: {integrity: sha512-/WQjhPJe3/ghaol/4Bq480JKXV/Rfw8nQdN7f41fM8VDHLcxKXou6QyXAh3EFr9/bVG3x74z1NWDkP87EiY8gA==}
    engines: {node: ^10.13.0 || ^12.13.0 || ^14.15.0 || >=15.0.0}
    dependencies:
      '@jest/fake-timers': 27.5.1
      '@jest/types': 27.5.1
      '@types/node': 20.2.5
      jest-mock: 27.5.1
    dev: false

  /@jest/expect-utils@29.5.0:
    resolution: {integrity: sha512-fmKzsidoXQT2KwnrwE0SQq3uj8Z763vzR8LnLBwC2qYWEFpjX8daRsk6rHUM1QvNlEW/UJXNXm59ztmJJWs2Mg==}
    engines: {node: ^14.15.0 || ^16.10.0 || >=18.0.0}
    dependencies:
      jest-get-type: 29.4.3
    dev: false

  /@jest/fake-timers@27.5.1:
    resolution: {integrity: sha512-/aPowoolwa07k7/oM3aASneNeBGCmGQsc3ugN4u6s4C/+s5M64MFo/+djTdiwcbQlRfFElGuDXWzaWj6QgKObQ==}
    engines: {node: ^10.13.0 || ^12.13.0 || ^14.15.0 || >=15.0.0}
    dependencies:
      '@jest/types': 27.5.1
      '@sinonjs/fake-timers': 8.1.0
      '@types/node': 20.2.5
      jest-message-util: 27.5.1
      jest-mock: 27.5.1
      jest-util: 27.5.1
    dev: false

  /@jest/globals@27.5.1:
    resolution: {integrity: sha512-ZEJNB41OBQQgGzgyInAv0UUfDDj3upmHydjieSxFvTRuZElrx7tXg/uVQ5hYVEwiXs3+aMsAeEc9X7xiSKCm4Q==}
    engines: {node: ^10.13.0 || ^12.13.0 || ^14.15.0 || >=15.0.0}
    dependencies:
      '@jest/environment': 27.5.1
      '@jest/types': 27.5.1
      expect: 27.5.1
    dev: false

  /@jest/reporters@27.5.1:
    resolution: {integrity: sha512-cPXh9hWIlVJMQkVk84aIvXuBB4uQQmFqZiacloFuGiP3ah1sbCxCosidXFDfqG8+6fO1oR2dTJTlsOy4VFmUfw==}
    engines: {node: ^10.13.0 || ^12.13.0 || ^14.15.0 || >=15.0.0}
    peerDependencies:
      node-notifier: ^8.0.1 || ^9.0.0 || ^10.0.0
    peerDependenciesMeta:
      node-notifier:
        optional: true
    dependencies:
      '@bcoe/v8-coverage': 0.2.3
      '@jest/console': 27.5.1
      '@jest/test-result': 27.5.1
      '@jest/transform': 27.5.1
      '@jest/types': 27.5.1
      '@types/node': 20.2.5
      chalk: 4.1.2
      collect-v8-coverage: 1.0.1
      exit: 0.1.2
      glob: 7.2.3
      graceful-fs: 4.2.11
      istanbul-lib-coverage: 3.2.0
      istanbul-lib-instrument: 5.2.1
      istanbul-lib-report: 3.0.0
      istanbul-lib-source-maps: 4.0.1
      istanbul-reports: 3.1.5
      jest-haste-map: 27.5.1
      jest-resolve: 27.5.1
      jest-util: 27.5.1
      jest-worker: 27.5.1
      slash: 3.0.0
      source-map: 0.6.1
      string-length: 4.0.2
      terminal-link: 2.1.1
      v8-to-istanbul: 8.1.1
    transitivePeerDependencies:
      - supports-color
    dev: false

  /@jest/schemas@28.1.3:
    resolution: {integrity: sha512-/l/VWsdt/aBXgjshLWOFyFt3IVdYypu5y2Wn2rOO1un6nkqIn8SLXzgIMYXFyYsRWDyF5EthmKJMIdJvk08grg==}
    engines: {node: ^12.13.0 || ^14.15.0 || ^16.10.0 || >=17.0.0}
    dependencies:
      '@sinclair/typebox': 0.24.51
    dev: false

  /@jest/schemas@29.4.3:
    resolution: {integrity: sha512-VLYKXQmtmuEz6IxJsrZwzG9NvtkQsWNnWMsKxqWNu3+CnfzJQhp0WDDKWLVV9hLKr0l3SLLFRqcYHjhtyuDVxg==}
    engines: {node: ^14.15.0 || ^16.10.0 || >=18.0.0}
    dependencies:
      '@sinclair/typebox': 0.25.24
    dev: false

  /@jest/source-map@27.5.1:
    resolution: {integrity: sha512-y9NIHUYF3PJRlHk98NdC/N1gl88BL08aQQgu4k4ZopQkCw9t9cV8mtl3TV8b/YCB8XaVTFrmUTAJvjsntDireg==}
    engines: {node: ^10.13.0 || ^12.13.0 || ^14.15.0 || >=15.0.0}
    dependencies:
      callsites: 3.1.0
      graceful-fs: 4.2.11
      source-map: 0.6.1
    dev: false

  /@jest/test-result@27.5.1:
    resolution: {integrity: sha512-EW35l2RYFUcUQxFJz5Cv5MTOxlJIQs4I7gxzi2zVU7PJhOwfYq1MdC5nhSmYjX1gmMmLPvB3sIaC+BkcHRBfag==}
    engines: {node: ^10.13.0 || ^12.13.0 || ^14.15.0 || >=15.0.0}
    dependencies:
      '@jest/console': 27.5.1
      '@jest/types': 27.5.1
      '@types/istanbul-lib-coverage': 2.0.4
      collect-v8-coverage: 1.0.1
    dev: false

  /@jest/test-result@28.1.3:
    resolution: {integrity: sha512-kZAkxnSE+FqE8YjW8gNuoVkkC9I7S1qmenl8sGcDOLropASP+BkcGKwhXoyqQuGOGeYY0y/ixjrd/iERpEXHNg==}
    engines: {node: ^12.13.0 || ^14.15.0 || ^16.10.0 || >=17.0.0}
    dependencies:
      '@jest/console': 28.1.3
      '@jest/types': 28.1.3
      '@types/istanbul-lib-coverage': 2.0.4
      collect-v8-coverage: 1.0.1
    dev: false

  /@jest/test-sequencer@27.5.1:
    resolution: {integrity: sha512-LCheJF7WB2+9JuCS7VB/EmGIdQuhtqjRNI9A43idHv3E4KltCTsPsLxvdaubFHSYwY/fNjMWjl6vNRhDiN7vpQ==}
    engines: {node: ^10.13.0 || ^12.13.0 || ^14.15.0 || >=15.0.0}
    dependencies:
      '@jest/test-result': 27.5.1
      graceful-fs: 4.2.11
      jest-haste-map: 27.5.1
      jest-runtime: 27.5.1
    transitivePeerDependencies:
      - supports-color
    dev: false

  /@jest/transform@27.5.1:
    resolution: {integrity: sha512-ipON6WtYgl/1329g5AIJVbUuEh0wZVbdpGwC99Jw4LwuoBNS95MVphU6zOeD9pDkon+LLbFL7lOQRapbB8SCHw==}
    engines: {node: ^10.13.0 || ^12.13.0 || ^14.15.0 || >=15.0.0}
    dependencies:
      '@babel/core': 7.22.1
      '@jest/types': 27.5.1
      babel-plugin-istanbul: 6.1.1
      chalk: 4.1.2
      convert-source-map: 1.9.0
      fast-json-stable-stringify: 2.1.0
      graceful-fs: 4.2.11
      jest-haste-map: 27.5.1
      jest-regex-util: 27.5.1
      jest-util: 27.5.1
      micromatch: 4.0.5
      pirates: 4.0.5
      slash: 3.0.0
      source-map: 0.6.1
      write-file-atomic: 3.0.3
    transitivePeerDependencies:
      - supports-color
    dev: false

  /@jest/types@27.5.1:
    resolution: {integrity: sha512-Cx46iJ9QpwQTjIdq5VJu2QTMMs3QlEjI0x1QbBP5W1+nMzyc2XmimiRR/CbX9TO0cPTeUlxWMOu8mslYsJ8DEw==}
    engines: {node: ^10.13.0 || ^12.13.0 || ^14.15.0 || >=15.0.0}
    dependencies:
      '@types/istanbul-lib-coverage': 2.0.4
      '@types/istanbul-reports': 3.0.1
      '@types/node': 20.2.5
      '@types/yargs': 16.0.5
      chalk: 4.1.2
    dev: false

  /@jest/types@28.1.3:
    resolution: {integrity: sha512-RyjiyMUZrKz/c+zlMFO1pm70DcIlST8AeWTkoUdZevew44wcNZQHsEVOiCVtgVnlFFD82FPaXycys58cf2muVQ==}
    engines: {node: ^12.13.0 || ^14.15.0 || ^16.10.0 || >=17.0.0}
    dependencies:
      '@jest/schemas': 28.1.3
      '@types/istanbul-lib-coverage': 2.0.4
      '@types/istanbul-reports': 3.0.1
      '@types/node': 20.2.5
      '@types/yargs': 17.0.24
      chalk: 4.1.2
    dev: false

  /@jest/types@29.5.0:
    resolution: {integrity: sha512-qbu7kN6czmVRc3xWFQcAN03RAUamgppVUdXrvl1Wr3jlNF93o9mJbGcDWrwGB6ht44u7efB1qCFgVQmca24Uog==}
    engines: {node: ^14.15.0 || ^16.10.0 || >=18.0.0}
    dependencies:
      '@jest/schemas': 29.4.3
      '@types/istanbul-lib-coverage': 2.0.4
      '@types/istanbul-reports': 3.0.1
      '@types/node': 20.2.5
      '@types/yargs': 17.0.24
      chalk: 4.1.2
    dev: false

  /@jridgewell/gen-mapping@0.3.3:
    resolution: {integrity: sha512-HLhSWOLRi875zjjMG/r+Nv0oCW8umGb0BgEhyX3dDX3egwZtB8PqLnjz3yedt8R5StBrzcg4aBpnh8UA9D1BoQ==}
    engines: {node: '>=6.0.0'}
    dependencies:
      '@jridgewell/set-array': 1.1.2
      '@jridgewell/sourcemap-codec': 1.4.15
      '@jridgewell/trace-mapping': 0.3.18

  /@jridgewell/resolve-uri@3.1.0:
    resolution: {integrity: sha512-F2msla3tad+Mfht5cJq7LSXcdudKTWCVYUgw6pLFOOHSTtZlj6SWNYAp+AhuqLmWdBO2X5hPrLcu8cVP8fy28w==}
    engines: {node: '>=6.0.0'}

  /@jridgewell/set-array@1.1.2:
    resolution: {integrity: sha512-xnkseuNADM0gt2bs+BvhO0p78Mk762YnZdsuzFV018NoG1Sj1SCQvpSqa7XUaTam5vAGasABV9qXASMKnFMwMw==}
    engines: {node: '>=6.0.0'}

  /@jridgewell/source-map@0.3.3:
    resolution: {integrity: sha512-b+fsZXeLYi9fEULmfBrhxn4IrPlINf8fiNarzTof004v3lFdntdwa9PF7vFJqm3mg7s+ScJMxXaE3Acp1irZcg==}
    dependencies:
      '@jridgewell/gen-mapping': 0.3.3
      '@jridgewell/trace-mapping': 0.3.18
    dev: false

  /@jridgewell/sourcemap-codec@1.4.14:
    resolution: {integrity: sha512-XPSJHWmi394fuUuzDnGz1wiKqWfo1yXecHQMRf2l6hztTO+nPru658AyDngaBe7isIxEkRsPR3FZh+s7iVa4Uw==}

  /@jridgewell/sourcemap-codec@1.4.15:
    resolution: {integrity: sha512-eF2rxCRulEKXHTRiDrDy6erMYWqNw4LPdQ8UQA4huuxaQsVeRPFl2oM8oDGxMFhJUWZf9McpLtJasDDZb/Bpeg==}

  /@jridgewell/trace-mapping@0.3.18:
    resolution: {integrity: sha512-w+niJYzMHdd7USdiH2U6869nqhD2nbfZXND5Yp93qIbEmnDNk7PD48o+YchRVpzMU7M6jVCbenTR7PA1FLQ9pA==}
    dependencies:
      '@jridgewell/resolve-uri': 3.1.0
      '@jridgewell/sourcemap-codec': 1.4.14

  /@leichtgewicht/ip-codec@2.0.4:
    resolution: {integrity: sha512-Hcv+nVC0kZnQ3tD9GVu5xSMR4VVYOteQIr/hwFPVEvPdlXqgGEuRjiheChHgdM+JyqdgNcmzZOX/tnl0JOiI7A==}
    dev: false

  /@mui/base@5.0.0-alpha.60(react-dom@17.0.2)(react@17.0.2):
    resolution: {integrity: sha512-J4cQoeqNFMaY6fgEJsT7meaLdYilA4R8wA53us3BT5NBP4puMeJLPK4rVSmpTsB8hf4Iyq+fosKzkcYRiKTctA==}
    engines: {node: '>=12.0.0'}
    peerDependencies:
      '@types/react': ^16.8.6 || ^17.0.0
      react: ^17.0.2
      react-dom: ^17.0.2
    peerDependenciesMeta:
      '@types/react':
        optional: true
    dependencies:
      '@babel/runtime': 7.22.3
      '@emotion/is-prop-valid': 1.2.1
      '@mui/utils': 5.13.1(react@17.0.2)
      '@popperjs/core': 2.11.8
      clsx: 1.2.1
      prop-types: 15.8.1
      react: 17.0.2
      react-dom: 17.0.2(react@17.0.2)
      react-is: 17.0.2
    dev: false

  /@mui/icons-material@5.11.16(@mui/material@5.2.4)(react@17.0.2):
    resolution: {integrity: sha512-oKkx9z9Kwg40NtcIajF9uOXhxiyTZrrm9nmIJ4UjkU2IdHpd4QVLbCc/5hZN/y0C6qzi2Zlxyr9TGddQx2vx2A==}
    engines: {node: '>=12.0.0'}
    peerDependencies:
      '@mui/material': ^5.0.0
      '@types/react': ^17.0.0 || ^18.0.0
      react: ^17.0.0 || ^18.0.0
    peerDependenciesMeta:
      '@types/react':
        optional: true
    dependencies:
      '@babel/runtime': 7.22.3
      '@mui/material': 5.2.4(@emotion/react@11.7.1)(@emotion/styled@11.6.0)(react-dom@17.0.2)(react@17.0.2)
      react: 17.0.2
    dev: false

  /@mui/material@5.2.4(@emotion/react@11.7.1)(@emotion/styled@11.6.0)(react-dom@17.0.2)(react@17.0.2):
    resolution: {integrity: sha512-W/0ib0aB5gKQ9DmEnYeKbmmzKBpn0039qDuQHjBE6RL5P1L5iYPGFMy4Es+7oQxiC77SuJ3xSOPsTpOW8QGDqw==}
    engines: {node: '>=12.0.0'}
    peerDependencies:
      '@emotion/react': ^11.5.0
      '@emotion/styled': ^11.3.0
      '@types/react': ^16.8.6 || ^17.0.0
      react: ^17.0.2
      react-dom: ^17.0.2
    peerDependenciesMeta:
      '@emotion/react':
        optional: true
      '@emotion/styled':
        optional: true
      '@types/react':
        optional: true
    dependencies:
      '@babel/runtime': 7.22.3
      '@emotion/react': 11.7.1(@babel/core@7.22.1)(react@17.0.2)
      '@emotion/styled': 11.6.0(@babel/core@7.22.1)(@emotion/react@11.7.1)(react@17.0.2)
      '@mui/base': 5.0.0-alpha.60(react-dom@17.0.2)(react@17.0.2)
      '@mui/system': 5.13.2(@emotion/react@11.7.1)(@emotion/styled@11.6.0)(react@17.0.2)
      '@mui/types': 7.2.4
      '@mui/utils': 5.13.1(react@17.0.2)
      '@types/react-transition-group': 4.4.6
      clsx: 1.2.1
      csstype: 3.1.2
      hoist-non-react-statics: 3.3.2
      prop-types: 15.8.1
      react: 17.0.2
      react-dom: 17.0.2(react@17.0.2)
      react-is: 17.0.2
      react-transition-group: 4.4.5(react-dom@17.0.2)(react@17.0.2)
    dev: false

  /@mui/private-theming@5.13.1(react@17.0.2):
    resolution: {integrity: sha512-HW4npLUD9BAkVppOUZHeO1FOKUJWAwbpy0VQoGe3McUYTlck1HezGHQCfBQ5S/Nszi7EViqiimECVl9xi+/WjQ==}
    engines: {node: '>=12.0.0'}
    peerDependencies:
      '@types/react': ^17.0.0 || ^18.0.0
      react: ^17.0.0 || ^18.0.0
    peerDependenciesMeta:
      '@types/react':
        optional: true
    dependencies:
      '@babel/runtime': 7.22.3
      '@mui/utils': 5.13.1(react@17.0.2)
      prop-types: 15.8.1
      react: 17.0.2
    dev: false

  /@mui/styled-engine@5.13.2(@emotion/react@11.7.1)(@emotion/styled@11.6.0)(react@17.0.2):
    resolution: {integrity: sha512-VCYCU6xVtXOrIN8lcbuPmoG+u7FYuOERG++fpY74hPpEWkyFQG97F+/XfTQVYzlR2m7nPjnwVUgATcTCMEaMvw==}
    engines: {node: '>=12.0.0'}
    peerDependencies:
      '@emotion/react': ^11.4.1
      '@emotion/styled': ^11.3.0
      react: ^17.0.0 || ^18.0.0
    peerDependenciesMeta:
      '@emotion/react':
        optional: true
      '@emotion/styled':
        optional: true
    dependencies:
      '@babel/runtime': 7.22.3
      '@emotion/cache': 11.11.0
      '@emotion/react': 11.7.1(@babel/core@7.22.1)(react@17.0.2)
      '@emotion/styled': 11.6.0(@babel/core@7.22.1)(@emotion/react@11.7.1)(react@17.0.2)
      csstype: 3.1.2
      prop-types: 15.8.1
      react: 17.0.2
    dev: false

  /@mui/system@5.13.2(@emotion/react@11.7.1)(@emotion/styled@11.6.0)(react@17.0.2):
    resolution: {integrity: sha512-TPyWmRJPt0JPVxacZISI4o070xEJ7ftxpVtu6LWuYVOUOINlhoGOclam4iV8PDT3EMQEHuUrwU49po34UdWLlw==}
    engines: {node: '>=12.0.0'}
    peerDependencies:
      '@emotion/react': ^11.5.0
      '@emotion/styled': ^11.3.0
      '@types/react': ^17.0.0 || ^18.0.0
      react: ^17.0.0 || ^18.0.0
    peerDependenciesMeta:
      '@emotion/react':
        optional: true
      '@emotion/styled':
        optional: true
      '@types/react':
        optional: true
    dependencies:
      '@babel/runtime': 7.22.3
      '@emotion/react': 11.7.1(@babel/core@7.22.1)(react@17.0.2)
      '@emotion/styled': 11.6.0(@babel/core@7.22.1)(@emotion/react@11.7.1)(react@17.0.2)
      '@mui/private-theming': 5.13.1(react@17.0.2)
      '@mui/styled-engine': 5.13.2(@emotion/react@11.7.1)(@emotion/styled@11.6.0)(react@17.0.2)
      '@mui/types': 7.2.4
      '@mui/utils': 5.13.1(react@17.0.2)
      clsx: 1.2.1
      csstype: 3.1.2
      prop-types: 15.8.1
      react: 17.0.2
    dev: false

  /@mui/types@7.2.4:
    resolution: {integrity: sha512-LBcwa8rN84bKF+f5sDyku42w1NTxaPgPyYKODsh01U1fVstTClbUoSA96oyRBnSNyEiAVjKm6Gwx9vjR+xyqHA==}
    peerDependencies:
      '@types/react': '*'
    peerDependenciesMeta:
      '@types/react':
        optional: true
    dev: false

  /@mui/utils@5.13.1(react@17.0.2):
    resolution: {integrity: sha512-6lXdWwmlUbEU2jUI8blw38Kt+3ly7xkmV9ljzY4Q20WhsJMWiNry9CX8M+TaP/HbtuyR8XKsdMgQW7h7MM3n3A==}
    engines: {node: '>=12.0.0'}
    peerDependencies:
      react: ^17.0.0 || ^18.0.0
    dependencies:
      '@babel/runtime': 7.22.3
      '@types/prop-types': 15.7.5
      '@types/react-is': 18.2.0
      prop-types: 15.8.1
      react: 17.0.2
      react-is: 18.2.0
    dev: false

  /@nicolo-ribaudo/eslint-scope-5-internals@5.1.1-v1:
    resolution: {integrity: sha512-54/JRvkLIzzDWshCWfuhadfrfZVPiElY8Fcgmg1HroEly/EDSszzhBAsarCux+D/kOslTRquNzuyGSmUSTTHGg==}
    dependencies:
      eslint-scope: 5.1.1
    dev: false

  /@nodelib/fs.scandir@2.1.5:
    resolution: {integrity: sha512-vq24Bq3ym5HEQm2NKCr3yXDwjc7vTsEThRDnkp2DK9p1uqLR+DHurm/NOTo0KG7HYHU7eppKZj3MyqYuMBf62g==}
    engines: {node: '>= 8'}
    dependencies:
      '@nodelib/fs.stat': 2.0.5
      run-parallel: 1.2.0

  /@nodelib/fs.stat@2.0.5:
    resolution: {integrity: sha512-RkhPPp2zrqDAQA/2jNhnztcPAlv64XdhIp7a7454A5ovI7Bukxgt7MX7udwAu3zg1DcpPU0rz3VV1SeaqvY4+A==}
    engines: {node: '>= 8'}

  /@nodelib/fs.walk@1.2.8:
    resolution: {integrity: sha512-oGB+UxlgWcgQkgwo8GcEGwemoTFt3FIO9ababBmaGwXIoBKZ+GTy0pP185beGg7Llih/NSHSV2XAs1lnznocSg==}
    engines: {node: '>= 8'}
    dependencies:
      '@nodelib/fs.scandir': 2.1.5
      fastq: 1.15.0

  /@pmmmwh/react-refresh-webpack-plugin@0.5.10(react-refresh@0.11.0)(webpack-dev-server@4.15.0)(webpack@5.85.1):
    resolution: {integrity: sha512-j0Ya0hCFZPd4x40qLzbhGsh9TMtdb+CJQiso+WxLOPNasohq9cc5SNUcwsZaRH6++Xh91Xkm/xHCkuIiIu0LUA==}
    engines: {node: '>= 10.13'}
    peerDependencies:
      '@types/webpack': 4.x || 5.x
      react-refresh: '>=0.10.0 <1.0.0'
      sockjs-client: ^1.4.0
      type-fest: '>=0.17.0 <4.0.0'
      webpack: '>=4.43.0 <6.0.0'
      webpack-dev-server: 3.x || 4.x
      webpack-hot-middleware: 2.x
      webpack-plugin-serve: 0.x || 1.x
    peerDependenciesMeta:
      '@types/webpack':
        optional: true
      sockjs-client:
        optional: true
      type-fest:
        optional: true
      webpack-dev-server:
        optional: true
      webpack-hot-middleware:
        optional: true
      webpack-plugin-serve:
        optional: true
    dependencies:
      ansi-html-community: 0.0.8
      common-path-prefix: 3.0.0
      core-js-pure: 3.30.2
      error-stack-parser: 2.1.4
      find-up: 5.0.0
      html-entities: 2.3.5
      loader-utils: 2.0.4
      react-refresh: 0.11.0
      schema-utils: 3.1.2
      source-map: 0.7.4
      webpack: 5.85.1
      webpack-dev-server: 4.15.0(webpack@5.85.1)
    dev: false

  /@popperjs/core@2.11.8:
    resolution: {integrity: sha512-P1st0aksCrn9sGZhp8GMYwBnQsbvAWsZAX44oXNNvLHGqAOcoVxmjZiohstwQ7SqKnbR47akdNi+uleWD8+g6A==}
    dev: false

  /@rollup/plugin-babel@5.3.1(@babel/core@7.22.1)(rollup@2.79.1):
    resolution: {integrity: sha512-WFfdLWU/xVWKeRQnKmIAQULUI7Il0gZnBIH/ZFO069wYIfPu+8zrfp/KMW0atmELoRDq8FbiP3VCss9MhCut7Q==}
    engines: {node: '>= 10.0.0'}
    peerDependencies:
      '@babel/core': ^7.0.0
      '@types/babel__core': ^7.1.9
      rollup: ^1.20.0||^2.0.0
    peerDependenciesMeta:
      '@types/babel__core':
        optional: true
    dependencies:
      '@babel/core': 7.22.1
      '@babel/helper-module-imports': 7.21.4
      '@rollup/pluginutils': 3.1.0(rollup@2.79.1)
      rollup: 2.79.1
    dev: false

  /@rollup/plugin-node-resolve@11.2.1(rollup@2.79.1):
    resolution: {integrity: sha512-yc2n43jcqVyGE2sqV5/YCmocy9ArjVAP/BeXyTtADTBBX6V0e5UMqwO8CdQ0kzjb6zu5P1qMzsScCMRvE9OlVg==}
    engines: {node: '>= 10.0.0'}
    peerDependencies:
      rollup: ^1.20.0||^2.0.0
    dependencies:
      '@rollup/pluginutils': 3.1.0(rollup@2.79.1)
      '@types/resolve': 1.17.1
      builtin-modules: 3.3.0
      deepmerge: 4.3.1
      is-module: 1.0.0
      resolve: 1.22.2
      rollup: 2.79.1
    dev: false

  /@rollup/plugin-replace@2.4.2(rollup@2.79.1):
    resolution: {integrity: sha512-IGcu+cydlUMZ5En85jxHH4qj2hta/11BHq95iHEyb2sbgiN0eCdzvUcHw5gt9pBL5lTi4JDYJ1acCoMGpTvEZg==}
    peerDependencies:
      rollup: ^1.20.0 || ^2.0.0
    dependencies:
      '@rollup/pluginutils': 3.1.0(rollup@2.79.1)
      magic-string: 0.25.9
      rollup: 2.79.1
    dev: false

  /@rollup/pluginutils@3.1.0(rollup@2.79.1):
    resolution: {integrity: sha512-GksZ6pr6TpIjHm8h9lSQ8pi8BE9VeubNT0OMJ3B5uZJ8pz73NPiqOtCog/x2/QzM1ENChPKxMDhiQuRHsqc+lg==}
    engines: {node: '>= 8.0.0'}
    peerDependencies:
      rollup: ^1.20.0||^2.0.0
    dependencies:
      '@types/estree': 0.0.39
      estree-walker: 1.0.1
      picomatch: 2.3.1
      rollup: 2.79.1
    dev: false

  /@rushstack/eslint-patch@1.3.0:
    resolution: {integrity: sha512-IthPJsJR85GhOkp3Hvp8zFOPK5ynKn6STyHa/WZpioK7E1aYDiBzpqQPrngc14DszIUkIrdd3k9Iu0XSzlP/1w==}
    dev: false

  /@sinclair/typebox@0.24.51:
    resolution: {integrity: sha512-1P1OROm/rdubP5aFDSZQILU0vrLCJ4fvHt6EoqHEM+2D/G5MK3bIaymUKLit8Js9gbns5UyJnkP/TZROLw4tUA==}
    dev: false

  /@sinclair/typebox@0.25.24:
    resolution: {integrity: sha512-XJfwUVUKDHF5ugKwIcxEgc9k8b7HbznCp6eUfWgu710hMPNIO4aw4/zB5RogDQz8nd6gyCDpU9O/m6qYEWY6yQ==}
    dev: false

  /@sinonjs/commons@1.8.6:
    resolution: {integrity: sha512-Ky+XkAkqPZSm3NLBeUng77EBQl3cmeJhITaGHdYH8kjVB+aun3S4XBRti2zt17mtt0mIUDiNxYeoJm6drVvBJQ==}
    dependencies:
      type-detect: 4.0.8
    dev: false

  /@sinonjs/fake-timers@8.1.0:
    resolution: {integrity: sha512-OAPJUAtgeINhh/TAlUID4QTs53Njm7xzddaVlEs/SXwgtiD1tW22zAB/W1wdqfrpmikgaWQ9Fw6Ws+hsiRm5Vg==}
    dependencies:
      '@sinonjs/commons': 1.8.6
    dev: false

  /@surma/rollup-plugin-off-main-thread@2.2.3:
    resolution: {integrity: sha512-lR8q/9W7hZpMWweNiAKU7NQerBnzQQLvi8qnTDU/fxItPhtZVMbPV3lbCwjhIlNBe9Bbr5V+KHshvWmVSG9cxQ==}
    dependencies:
      ejs: 3.1.9
      json5: 2.2.3
      magic-string: 0.25.9
      string.prototype.matchall: 4.0.8
    dev: false

  /@svgr/babel-plugin-add-jsx-attribute@5.4.0:
    resolution: {integrity: sha512-ZFf2gs/8/6B8PnSofI0inYXr2SDNTDScPXhN7k5EqD4aZ3gi6u+rbmZHVB8IM3wDyx8ntKACZbtXSm7oZGRqVg==}
    engines: {node: '>=10'}
    dev: false

  /@svgr/babel-plugin-remove-jsx-attribute@5.4.0:
    resolution: {integrity: sha512-yaS4o2PgUtwLFGTKbsiAy6D0o3ugcUhWK0Z45umJ66EPWunAz9fuFw2gJuje6wqQvQWOTJvIahUwndOXb7QCPg==}
    engines: {node: '>=10'}
    dev: false

  /@svgr/babel-plugin-remove-jsx-empty-expression@5.0.1:
    resolution: {integrity: sha512-LA72+88A11ND/yFIMzyuLRSMJ+tRKeYKeQ+mR3DcAZ5I4h5CPWN9AHyUzJbWSYp/u2u0xhmgOe0+E41+GjEueA==}
    engines: {node: '>=10'}
    dev: false

  /@svgr/babel-plugin-replace-jsx-attribute-value@5.0.1:
    resolution: {integrity: sha512-PoiE6ZD2Eiy5mK+fjHqwGOS+IXX0wq/YDtNyIgOrc6ejFnxN4b13pRpiIPbtPwHEc+NT2KCjteAcq33/F1Y9KQ==}
    engines: {node: '>=10'}
    dev: false

  /@svgr/babel-plugin-svg-dynamic-title@5.4.0:
    resolution: {integrity: sha512-zSOZH8PdZOpuG1ZVx/cLVePB2ibo3WPpqo7gFIjLV9a0QsuQAzJiwwqmuEdTaW2pegyBE17Uu15mOgOcgabQZg==}
    engines: {node: '>=10'}
    dev: false

  /@svgr/babel-plugin-svg-em-dimensions@5.4.0:
    resolution: {integrity: sha512-cPzDbDA5oT/sPXDCUYoVXEmm3VIoAWAPT6mSPTJNbQaBNUuEKVKyGH93oDY4e42PYHRW67N5alJx/eEol20abw==}
    engines: {node: '>=10'}
    dev: false

  /@svgr/babel-plugin-transform-react-native-svg@5.4.0:
    resolution: {integrity: sha512-3eYP/SaopZ41GHwXma7Rmxcv9uRslRDTY1estspeB1w1ueZWd/tPlMfEOoccYpEMZU3jD4OU7YitnXcF5hLW2Q==}
    engines: {node: '>=10'}
    dev: false

  /@svgr/babel-plugin-transform-svg-component@5.5.0:
    resolution: {integrity: sha512-q4jSH1UUvbrsOtlo/tKcgSeiCHRSBdXoIoqX1pgcKK/aU3JD27wmMKwGtpB8qRYUYoyXvfGxUVKchLuR5pB3rQ==}
    engines: {node: '>=10'}
    dev: false

  /@svgr/babel-preset@5.5.0:
    resolution: {integrity: sha512-4FiXBjvQ+z2j7yASeGPEi8VD/5rrGQk4Xrq3EdJmoZgz/tpqChpo5hgXDvmEauwtvOc52q8ghhZK4Oy7qph4ig==}
    engines: {node: '>=10'}
    dependencies:
      '@svgr/babel-plugin-add-jsx-attribute': 5.4.0
      '@svgr/babel-plugin-remove-jsx-attribute': 5.4.0
      '@svgr/babel-plugin-remove-jsx-empty-expression': 5.0.1
      '@svgr/babel-plugin-replace-jsx-attribute-value': 5.0.1
      '@svgr/babel-plugin-svg-dynamic-title': 5.4.0
      '@svgr/babel-plugin-svg-em-dimensions': 5.4.0
      '@svgr/babel-plugin-transform-react-native-svg': 5.4.0
      '@svgr/babel-plugin-transform-svg-component': 5.5.0
    dev: false

  /@svgr/core@5.5.0:
    resolution: {integrity: sha512-q52VOcsJPvV3jO1wkPtzTuKlvX7Y3xIcWRpCMtBF3MrteZJtBfQw/+u0B1BHy5ColpQc1/YVTrPEtSYIMNZlrQ==}
    engines: {node: '>=10'}
    dependencies:
      '@svgr/plugin-jsx': 5.5.0
      camelcase: 6.3.0
      cosmiconfig: 7.1.0
    transitivePeerDependencies:
      - supports-color
    dev: false

  /@svgr/hast-util-to-babel-ast@5.5.0:
    resolution: {integrity: sha512-cAaR/CAiZRB8GP32N+1jocovUtvlj0+e65TB50/6Lcime+EA49m/8l+P2ko+XPJ4dw3xaPS3jOL4F2X4KWxoeQ==}
    engines: {node: '>=10'}
    dependencies:
      '@babel/types': 7.22.4
    dev: false

  /@svgr/plugin-jsx@5.5.0:
    resolution: {integrity: sha512-V/wVh33j12hGh05IDg8GpIUXbjAPnTdPTKuP4VNLggnwaHMPNQNae2pRnyTAILWCQdz5GyMqtO488g7CKM8CBA==}
    engines: {node: '>=10'}
    dependencies:
      '@babel/core': 7.22.1
      '@svgr/babel-preset': 5.5.0
      '@svgr/hast-util-to-babel-ast': 5.5.0
      svg-parser: 2.0.4
    transitivePeerDependencies:
      - supports-color
    dev: false

  /@svgr/plugin-svgo@5.5.0:
    resolution: {integrity: sha512-r5swKk46GuQl4RrVejVwpeeJaydoxkdwkM1mBKOgJLBUJPGaLci6ylg/IjhrRsREKDkr4kbMWdgOtbXEh0fyLQ==}
    engines: {node: '>=10'}
    dependencies:
      cosmiconfig: 7.1.0
      deepmerge: 4.3.1
      svgo: 1.3.2
    dev: false

  /@svgr/webpack@5.5.0:
    resolution: {integrity: sha512-DOBOK255wfQxguUta2INKkzPj6AIS6iafZYiYmHn6W3pHlycSRRlvWKCfLDG10fXfLWqE3DJHgRUOyJYmARa7g==}
    engines: {node: '>=10'}
    dependencies:
      '@babel/core': 7.22.1
      '@babel/plugin-transform-react-constant-elements': 7.22.3(@babel/core@7.22.1)
      '@babel/preset-env': 7.22.4(@babel/core@7.22.1)
      '@babel/preset-react': 7.22.3(@babel/core@7.22.1)
      '@svgr/core': 5.5.0
      '@svgr/plugin-jsx': 5.5.0
      '@svgr/plugin-svgo': 5.5.0
      loader-utils: 2.0.4
    transitivePeerDependencies:
      - supports-color
    dev: false

  /@testing-library/dom@8.20.0:
    resolution: {integrity: sha512-d9ULIT+a4EXLX3UU8FBjauG9NnsZHkHztXoIcTsOKoOw030fyjheN9svkTULjJxtYag9DZz5Jz5qkWZDPxTFwA==}
    engines: {node: '>=12'}
    dependencies:
      '@babel/code-frame': 7.21.4
      '@babel/runtime': 7.22.3
      '@types/aria-query': 5.0.1
      aria-query: 5.1.3
      chalk: 4.1.2
      dom-accessibility-api: 0.5.16
      lz-string: 1.5.0
      pretty-format: 27.5.1
    dev: false

  /@testing-library/dom@9.3.0:
    resolution: {integrity: sha512-Dffe68pGwI6WlLRYR2I0piIkyole9cSBH5jGQKCGMRpHW5RHCqAUaqc2Kv0tUyd4dU4DLPKhJIjyKOnjv4tuUw==}
    engines: {node: '>=14'}
    dependencies:
      '@babel/code-frame': 7.21.4
      '@babel/runtime': 7.22.3
      '@types/aria-query': 5.0.1
      aria-query: 5.1.3
      chalk: 4.1.2
      dom-accessibility-api: 0.5.16
      lz-string: 1.5.0
      pretty-format: 27.5.1
    dev: false

  /@testing-library/jest-dom@5.16.1:
    resolution: {integrity: sha512-ajUJdfDIuTCadB79ukO+0l8O+QwN0LiSxDaYUTI4LndbbUsGi6rWU1SCexXzBA2NSjlVB9/vbkasQIL3tmPBjw==}
    engines: {node: '>=8', npm: '>=6', yarn: '>=1'}
    dependencies:
      '@babel/runtime': 7.22.3
      '@types/testing-library__jest-dom': 5.14.6
      aria-query: 5.1.3
      chalk: 3.0.0
      css: 3.0.0
      css.escape: 1.5.1
      dom-accessibility-api: 0.5.16
      lodash: 4.17.21
      redent: 3.0.0
    dev: false

  /@testing-library/react@12.1.2(react-dom@17.0.2)(react@17.0.2):
    resolution: {integrity: sha512-ihQiEOklNyHIpo2Y8FREkyD1QAea054U0MVbwH1m8N9TxeFz+KoJ9LkqoKqJlzx2JDm56DVwaJ1r36JYxZM05g==}
    engines: {node: '>=12'}
    peerDependencies:
      react: '*'
      react-dom: '*'
    dependencies:
      '@babel/runtime': 7.22.3
      '@testing-library/dom': 8.20.0
      react: 17.0.2
      react-dom: 17.0.2(react@17.0.2)
    dev: false

  /@testing-library/user-event@13.5.0(@testing-library/dom@9.3.0):
    resolution: {integrity: sha512-5Kwtbo3Y/NowpkbRuSepbyMFkZmHgD+vPzYB/RJ4oxt5Gj/avFFBYjhw27cqSVPVw/3a67NK1PbiIr9k4Gwmdg==}
    engines: {node: '>=10', npm: '>=6'}
    peerDependencies:
      '@testing-library/dom': '>=7.21.4'
    dependencies:
      '@babel/runtime': 7.22.3
      '@testing-library/dom': 9.3.0
    dev: false

  /@tootallnate/once@1.1.2:
    resolution: {integrity: sha512-RbzJvlNzmRq5c3O09UipeuXno4tA1FE6ikOjxZK0tuxVv3412l64l5t1W5pj4+rJq9vpkm/kwiR07aZXnsKPxw==}
    engines: {node: '>= 6'}
    dev: false

  /@trysound/sax@0.2.0:
    resolution: {integrity: sha512-L7z9BgrNEcYyUYtF+HaEfiS5ebkh9jXqbszz7pC0hRBPaatV0XjSD3+eHrpqFemQfgwiFF0QPIarnIihIDn7OA==}
    engines: {node: '>=10.13.0'}
    dev: false

  /@types/aria-query@5.0.1:
    resolution: {integrity: sha512-XTIieEY+gvJ39ChLcB4If5zHtPxt3Syj5rgZR+e1ctpmK8NjPf0zFqsz4JpLJT0xla9GFDKjy8Cpu331nrmE1Q==}
    dev: false

  /@types/babel__core@7.20.1:
    resolution: {integrity: sha512-aACu/U/omhdk15O4Nfb+fHgH/z3QsfQzpnvRZhYhThms83ZnAOZz7zZAWO7mn2yyNQaA4xTO8GLK3uqFU4bYYw==}
    dependencies:
      '@babel/parser': 7.22.4
      '@babel/types': 7.22.4
      '@types/babel__generator': 7.6.4
      '@types/babel__template': 7.4.1
      '@types/babel__traverse': 7.20.1
    dev: false

  /@types/babel__generator@7.6.4:
    resolution: {integrity: sha512-tFkciB9j2K755yrTALxD44McOrk+gfpIpvC3sxHjRawj6PfnQxrse4Clq5y/Rq+G3mrBurMax/lG8Qn2t9mSsg==}
    dependencies:
      '@babel/types': 7.22.4
    dev: false

  /@types/babel__template@7.4.1:
    resolution: {integrity: sha512-azBFKemX6kMg5Io+/rdGT0dkGreboUVR0Cdm3fz9QJWpaQGJRQXl7C+6hOTCZcMll7KFyEQpgbYI2lHdsS4U7g==}
    dependencies:
      '@babel/parser': 7.22.4
      '@babel/types': 7.22.4
    dev: false

  /@types/babel__traverse@7.20.1:
    resolution: {integrity: sha512-MitHFXnhtgwsGZWtT68URpOvLN4EREih1u3QtQiN4VdAxWKRVvGCSvw/Qth0M0Qq3pJpnGOu5JaM/ydK7OGbqg==}
    dependencies:
      '@babel/types': 7.22.4
    dev: false

  /@types/body-parser@1.19.2:
    resolution: {integrity: sha512-ALYone6pm6QmwZoAgeyNksccT9Q4AWZQ6PvfwR37GT6r6FWUPguq6sUmNGSMV2Wr761oQoBxwGGa6DR5o1DC9g==}
    dependencies:
      '@types/connect': 3.4.35
      '@types/node': 20.2.5
    dev: false

  /@types/bonjour@3.5.10:
    resolution: {integrity: sha512-p7ienRMiS41Nu2/igbJxxLDWrSZ0WxM8UQgCeO9KhoVF7cOVFkrKsiDr1EsJIla8vV3oEEjGcz11jc5yimhzZw==}
    dependencies:
      '@types/node': 20.2.5
    dev: false

  /@types/connect-history-api-fallback@1.5.0:
    resolution: {integrity: sha512-4x5FkPpLipqwthjPsF7ZRbOv3uoLUFkTA9G9v583qi4pACvq0uTELrB8OLUzPWUI4IJIyvM85vzkV1nyiI2Lig==}
    dependencies:
      '@types/express-serve-static-core': 4.17.35
      '@types/node': 20.2.5
    dev: false

  /@types/connect@3.4.35:
    resolution: {integrity: sha512-cdeYyv4KWoEgpBISTxWvqYsVy444DOqehiF3fM3ne10AmJ62RSyNkUnxMJXHQWRQQX2eR94m5y1IZyDwBjV9FQ==}
    dependencies:
      '@types/node': 20.2.5
    dev: false

  /@types/eslint-scope@3.7.4:
    resolution: {integrity: sha512-9K4zoImiZc3HlIp6AVUDE4CWYx22a+lhSZMYNpbjW04+YF0KWj4pJXnEMjdnFTiQibFFmElcsasJXDbdI/EPhA==}
    dependencies:
      '@types/eslint': 8.40.0
      '@types/estree': 1.0.1
    dev: false

  /@types/eslint@8.40.0:
    resolution: {integrity: sha512-nbq2mvc/tBrK9zQQuItvjJl++GTN5j06DaPtp3hZCpngmG6Q3xoyEmd0TwZI0gAy/G1X0zhGBbr2imsGFdFV0g==}
    dependencies:
      '@types/estree': 1.0.1
      '@types/json-schema': 7.0.12
    dev: false

  /@types/estree@0.0.39:
    resolution: {integrity: sha512-EYNwp3bU+98cpU4lAWYYL7Zz+2gryWH1qbdDTidVd6hkiR6weksdbMadyXKXNPEkQFhXM+hVO9ZygomHXp+AIw==}
    dev: false

  /@types/estree@1.0.1:
    resolution: {integrity: sha512-LG4opVs2ANWZ1TJoKc937iMmNstM/d0ae1vNbnBvBhqCSezgVUOzcLCqbI5elV8Vy6WKwKjaqR+zO9VKirBBCA==}
    dev: false

  /@types/express-serve-static-core@4.17.35:
    resolution: {integrity: sha512-wALWQwrgiB2AWTT91CB62b6Yt0sNHpznUXeZEcnPU3DRdlDIz74x8Qg1UUYKSVFi+va5vKOLYRBI1bRKiLLKIg==}
    dependencies:
      '@types/node': 20.2.5
      '@types/qs': 6.9.7
      '@types/range-parser': 1.2.4
      '@types/send': 0.17.1
    dev: false

  /@types/express@4.17.17:
    resolution: {integrity: sha512-Q4FmmuLGBG58btUnfS1c1r/NQdlp3DMfGDGig8WhfpA2YRUtEkxAjkZb0yvplJGYdF1fsQ81iMDcH24sSCNC/Q==}
    dependencies:
      '@types/body-parser': 1.19.2
      '@types/express-serve-static-core': 4.17.35
      '@types/qs': 6.9.7
      '@types/serve-static': 1.15.1
    dev: false

  /@types/graceful-fs@4.1.6:
    resolution: {integrity: sha512-Sig0SNORX9fdW+bQuTEovKj3uHcUL6LQKbCrrqb1X7J6/ReAbhCXRAhc+SMejhLELFj2QcyuxmUooZ4bt5ReSw==}
    dependencies:
      '@types/node': 20.2.5
    dev: false

  /@types/html-minifier-terser@6.1.0:
    resolution: {integrity: sha512-oh/6byDPnL1zeNXFrDXFLyZjkr1MsBG667IM792caf1L2UPOOMf65NFzjUH/ltyfwjAGfs1rsX1eftK0jC/KIg==}
    dev: false

  /@types/http-proxy@1.17.11:
    resolution: {integrity: sha512-HC8G7c1WmaF2ekqpnFq626xd3Zz0uvaqFmBJNRZCGEZCXkvSdJoNFn/8Ygbd9fKNQj8UzLdCETaI0UWPAjK7IA==}
    dependencies:
      '@types/node': 20.2.5
    dev: false

  /@types/istanbul-lib-coverage@2.0.4:
    resolution: {integrity: sha512-z/QT1XN4K4KYuslS23k62yDIDLwLFkzxOuMplDtObz0+y7VqJCaO2o+SPwHCvLFZh7xazvvoor2tA/hPz9ee7g==}
    dev: false

  /@types/istanbul-lib-report@3.0.0:
    resolution: {integrity: sha512-plGgXAPfVKFoYfa9NpYDAkseG+g6Jr294RqeqcqDixSbU34MZVJRi/P+7Y8GDpzkEwLaGZZOpKIEmeVZNtKsrg==}
    dependencies:
      '@types/istanbul-lib-coverage': 2.0.4
    dev: false

  /@types/istanbul-reports@3.0.1:
    resolution: {integrity: sha512-c3mAZEuK0lvBp8tmuL74XRKn1+y2dcwOUpH7x4WrF6gk1GIgiluDRgMYQtw2OFcBvAJWlt6ASU3tSqxp0Uu0Aw==}
    dependencies:
      '@types/istanbul-lib-report': 3.0.0
    dev: false

  /@types/jest@29.5.2:
    resolution: {integrity: sha512-mSoZVJF5YzGVCk+FsDxzDuH7s+SCkzrgKZzf0Z0T2WudhBUPoF6ktoTPC4R0ZoCPCV5xUvuU6ias5NvxcBcMMg==}
    dependencies:
      expect: 29.5.0
      pretty-format: 29.5.0
    dev: false

  /@types/json-schema@7.0.12:
    resolution: {integrity: sha512-Hr5Jfhc9eYOQNPYO5WLDq/n4jqijdHNlDXjuAQkkt+mWdQR+XJToOHrsD4cPaMXpn6KO7y2+wM8AZEs8VpBLVA==}
    dev: false

  /@types/json5@0.0.29:
    resolution: {integrity: sha512-dRLjCWHYg4oaA77cxO64oO+7JwCwnIzkZPdrrC71jQmQtlhM556pwKo5bUzqvZndkVbeFLIIi+9TC40JNF5hNQ==}
    dev: false

  /@types/mime@1.3.2:
    resolution: {integrity: sha512-YATxVxgRqNH6nHEIsvg6k2Boc1JHI9ZbH5iWFFv/MTkchz3b1ieGDa5T0a9RznNdI0KhVbdbWSN+KWWrQZRxTw==}
    dev: false

  /@types/mime@3.0.1:
    resolution: {integrity: sha512-Y4XFY5VJAuw0FgAqPNd6NNoV44jbq9Bz2L7Rh/J6jLTiHBSBJa9fxqQIvkIld4GsoDOcCbvzOUAbLPsSKKg+uA==}
    dev: false

  /@types/node@20.2.5:
    resolution: {integrity: sha512-JJulVEQXmiY9Px5axXHeYGLSjhkZEnD+MDPDGbCbIAbMslkKwmygtZFy1X6s/075Yo94sf8GuSlFfPzysQrWZQ==}
    dev: false

  /@types/parse-json@4.0.0:
    resolution: {integrity: sha512-//oorEZjL6sbPcKUaCdIGlIUeH26mgzimjBB77G6XRgnDl/L5wOnpyBGRe/Mmf5CVW3PwEBE1NjiMZ/ssFh4wA==}
    dev: false

  /@types/prettier@2.7.3:
    resolution: {integrity: sha512-+68kP9yzs4LMp7VNh8gdzMSPZFL44MLGqiHWvttYJe+6qnuVr4Ek9wSBQoveqY/r+LwjCcU29kNVkidwim+kYA==}
    dev: false

  /@types/prop-types@15.7.5:
    resolution: {integrity: sha512-JCB8C6SnDoQf0cNycqd/35A7MjcnK+ZTqE7judS6o7utxUCg6imJg3QK2qzHKszlTjcj2cn+NwMB2i96ubpj7w==}
    dev: false

  /@types/q@1.5.5:
    resolution: {integrity: sha512-L28j2FcJfSZOnL1WBjDYp2vUHCeIFlyYI/53EwD/rKUBQ7MtUUfbQWiyKJGpcnv4/WgrhWsFKrcPstcAt/J0tQ==}
    dev: false

  /@types/qs@6.9.7:
    resolution: {integrity: sha512-FGa1F62FT09qcrueBA6qYTrJPVDzah9a+493+o2PCXsesWHIn27G98TsSMs3WPNbZIEj4+VJf6saSFpvD+3Zsw==}
    dev: false

  /@types/range-parser@1.2.4:
    resolution: {integrity: sha512-EEhsLsD6UsDM1yFhAvy0Cjr6VwmpMWqFBCb9w07wVugF7w9nfajxLuVmngTIpgS6svCnm6Vaw+MZhoDCKnOfsw==}
    dev: false

  /@types/react-is@18.2.0:
    resolution: {integrity: sha512-1vz2yObaQkLL7YFe/pme2cpvDsCwI1WXIfL+5eLz0MI9gFG24Re16RzUsI8t9XZn9ZWvgLNDrJBmrqXJO7GNQQ==}
    dependencies:
      '@types/react': 18.2.8
    dev: false

  /@types/react-transition-group@4.4.6:
    resolution: {integrity: sha512-VnCdSxfcm08KjsJVQcfBmhEQAPnLB8G08hAxn39azX1qYBQ/5RVQuoHuKIcfKOdncuaUvEpFKFzEvbtIMsfVew==}
    dependencies:
      '@types/react': 18.2.8
    dev: false

  /@types/react@18.2.8:
    resolution: {integrity: sha512-lTyWUNrd8ntVkqycEEplasWy2OxNlShj3zqS0LuB1ENUGis5HodmhM7DtCoUGbxj3VW/WsGA0DUhpG6XrM7gPA==}
    dependencies:
      '@types/prop-types': 15.7.5
      '@types/scheduler': 0.16.3
      csstype: 3.1.2
    dev: false

  /@types/resolve@1.17.1:
    resolution: {integrity: sha512-yy7HuzQhj0dhGpD8RLXSZWEkLsV9ibvxvi6EiJ3bkqLAO1RGo0WbkWQiwpRlSFymTJRz0d3k5LM3kkx8ArDbLw==}
    dependencies:
      '@types/node': 20.2.5
    dev: false

  /@types/retry@0.12.0:
    resolution: {integrity: sha512-wWKOClTTiizcZhXnPY4wikVAwmdYHp8q6DmC+EJUzAMsycb7HB32Kh9RN4+0gExjmPmZSAQjgURXIGATPegAvA==}
    dev: false

  /@types/scheduler@0.16.3:
    resolution: {integrity: sha512-5cJ8CB4yAx7BH1oMvdU0Jh9lrEXyPkar6F9G/ERswkCuvP4KQZfZkSjcMbAICCpQTN4OuZn8tz0HiKv9TGZgrQ==}
    dev: false

  /@types/semver@7.5.0:
    resolution: {integrity: sha512-G8hZ6XJiHnuhQKR7ZmysCeJWE08o8T0AXtk5darsCaTVsYZhhgUrq53jizaR2FvsoeCwJhlmwTjkXBY5Pn/ZHw==}
    dev: false

  /@types/send@0.17.1:
    resolution: {integrity: sha512-Cwo8LE/0rnvX7kIIa3QHCkcuF21c05Ayb0ZfxPiv0W8VRiZiNW/WuRupHKpqqGVGf7SUA44QSOUKaEd9lIrd/Q==}
    dependencies:
      '@types/mime': 1.3.2
      '@types/node': 20.2.5
    dev: false

  /@types/serve-index@1.9.1:
    resolution: {integrity: sha512-d/Hs3nWDxNL2xAczmOVZNj92YZCS6RGxfBPjKzuu/XirCgXdpKEb88dYNbrYGint6IVWLNP+yonwVAuRC0T2Dg==}
    dependencies:
      '@types/express': 4.17.17
    dev: false

  /@types/serve-static@1.15.1:
    resolution: {integrity: sha512-NUo5XNiAdULrJENtJXZZ3fHtfMolzZwczzBbnAeBbqBwG+LaG6YaJtuwzwGSQZ2wsCrxjEhNNjAkKigy3n8teQ==}
    dependencies:
      '@types/mime': 3.0.1
      '@types/node': 20.2.5
    dev: false

  /@types/sockjs@0.3.33:
    resolution: {integrity: sha512-f0KEEe05NvUnat+boPTZ0dgaLZ4SfSouXUgv5noUiefG2ajgKjmETo9ZJyuqsl7dfl2aHlLJUiki6B4ZYldiiw==}
    dependencies:
      '@types/node': 20.2.5
    dev: false

  /@types/stack-utils@2.0.1:
    resolution: {integrity: sha512-Hl219/BT5fLAaz6NDkSuhzasy49dwQS/DSdu4MdggFB8zcXv7vflBI3xp7FEmkmdDkBUI2bPUNeMttp2knYdxw==}
    dev: false

  /@types/testing-library__jest-dom@5.14.6:
    resolution: {integrity: sha512-FkHXCb+ikSoUP4Y4rOslzTdX5sqYwMxfefKh1GmZ8ce1GOkEHntSp6b5cGadmNfp5e4BMEWOMx+WSKd5/MqlDA==}
    dependencies:
      '@types/jest': 29.5.2
    dev: false

  /@types/trusted-types@2.0.3:
    resolution: {integrity: sha512-NfQ4gyz38SL8sDNrSixxU2Os1a5xcdFxipAFxYEuLUlvU2uDwS4NUpsImcf1//SlWItCVMMLiylsxbmNMToV/g==}
    dev: false

  /@types/ws@8.5.4:
    resolution: {integrity: sha512-zdQDHKUgcX/zBc4GrwsE/7dVdAD8JR4EuiAXiiUhhfyIJXXb2+PrGshFyeXWQPMmmZ2XxgaqclgpIC7eTXc1mg==}
    dependencies:
      '@types/node': 20.2.5
    dev: false

  /@types/yargs-parser@21.0.0:
    resolution: {integrity: sha512-iO9ZQHkZxHn4mSakYV0vFHAVDyEOIJQrV2uZ06HxEPcx+mt8swXoZHIbaaJ2crJYFfErySgktuTZ3BeLz+XmFA==}
    dev: false

  /@types/yargs@16.0.5:
    resolution: {integrity: sha512-AxO/ADJOBFJScHbWhq2xAhlWP24rY4aCEG/NFaMvbT3X2MgRsLjhjQwsn0Zi5zn0LG9jUhCCZMeX9Dkuw6k+vQ==}
    dependencies:
      '@types/yargs-parser': 21.0.0
    dev: false

  /@types/yargs@17.0.24:
    resolution: {integrity: sha512-6i0aC7jV6QzQB8ne1joVZ0eSFIstHsCrobmOtghM11yGlH0j43FKL2UhWdELkyps0zuf7qVTUVCCR+tgSlyLLw==}
    dependencies:
      '@types/yargs-parser': 21.0.0
    dev: false

  /@typescript-eslint/eslint-plugin@5.59.9(@typescript-eslint/parser@5.59.9)(eslint@8.42.0)(typescript@5.1.3):
    resolution: {integrity: sha512-4uQIBq1ffXd2YvF7MAvehWKW3zVv/w+mSfRAu+8cKbfj3nwzyqJLNcZJpQ/WZ1HLbJDiowwmQ6NO+63nCA+fqA==}
    engines: {node: ^12.22.0 || ^14.17.0 || >=16.0.0}
    peerDependencies:
      '@typescript-eslint/parser': ^5.0.0
      eslint: ^6.0.0 || ^7.0.0 || ^8.0.0
      typescript: '*'
    peerDependenciesMeta:
      typescript:
        optional: true
    dependencies:
      '@eslint-community/regexpp': 4.5.1
      '@typescript-eslint/parser': 5.59.9(eslint@8.42.0)(typescript@5.1.3)
      '@typescript-eslint/scope-manager': 5.59.9
      '@typescript-eslint/type-utils': 5.59.9(eslint@8.42.0)(typescript@5.1.3)
      '@typescript-eslint/utils': 5.59.9(eslint@8.42.0)(typescript@5.1.3)
      debug: 4.3.4
      eslint: 8.42.0
      grapheme-splitter: 1.0.4
      ignore: 5.2.4
      natural-compare-lite: 1.4.0
      semver: 7.5.1
      tsutils: 3.21.0(typescript@5.1.3)
      typescript: 5.1.3
    transitivePeerDependencies:
      - supports-color
    dev: false

  /@typescript-eslint/experimental-utils@5.59.9(eslint@8.42.0)(typescript@5.1.3):
    resolution: {integrity: sha512-eZTK/Ci0QAqNc/q2MqMwI2+QI5ZI9HM12FcfGwbEvKif5ev/CIIYLmrlckvgPrC8XSbl39HtErR5NJiQkRkvWg==}
    engines: {node: ^12.22.0 || ^14.17.0 || >=16.0.0}
    peerDependencies:
      eslint: ^6.0.0 || ^7.0.0 || ^8.0.0
    dependencies:
      '@typescript-eslint/utils': 5.59.9(eslint@8.42.0)(typescript@5.1.3)
      eslint: 8.42.0
    transitivePeerDependencies:
      - supports-color
      - typescript
    dev: false

  /@typescript-eslint/parser@5.59.9(eslint@8.42.0)(typescript@5.1.3):
    resolution: {integrity: sha512-FsPkRvBtcLQ/eVK1ivDiNYBjn3TGJdXy2fhXX+rc7czWl4ARwnpArwbihSOHI2Peg9WbtGHrbThfBUkZZGTtvQ==}
    engines: {node: ^12.22.0 || ^14.17.0 || >=16.0.0}
    peerDependencies:
      eslint: ^6.0.0 || ^7.0.0 || ^8.0.0
      typescript: '*'
    peerDependenciesMeta:
      typescript:
        optional: true
    dependencies:
      '@typescript-eslint/scope-manager': 5.59.9
      '@typescript-eslint/types': 5.59.9
      '@typescript-eslint/typescript-estree': 5.59.9(typescript@5.1.3)
      debug: 4.3.4
      eslint: 8.42.0
      typescript: 5.1.3
    transitivePeerDependencies:
      - supports-color
    dev: false
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
