farisrfp/smart-pju-device/firmware/src/LoRaWAN/loramac.cpp

#include "loramac.h"

// Fill in your AppEUI, DevEUI and AppKey
#include "secrets.h"

const lmic_pinmap lmic_pins = {
    .nss = PIN_NSS,
    .rxtx = LMIC_UNUSED_PIN,
    .rst = PIN_RST,
    .dio = {PIN_DIO0, PIN_DIO1, PIN_DIO2},
};

static osjob_t sendjob;
static int spreadFactor = DR_SF7;
static int joinStatus = EV_JOINING;
static const unsigned TX_INTERVAL = 15;

void os_getArtEui(u1_t *buf) {
    uint8_t artEui[8];

    if (EEPROM.readBytes(ADDR_APPEUI, artEui, 8) == 8) {
        memcpy(buf, artEui, 8);
    } else {
        memcpy_P(buf, APPEUI, 8);
    }
}

void os_getDevEui(u1_t *buf) {
    uint8_t devEui[8];

    if (EEPROM.readBytes(ADDR_DEVEUI, devEui, 8) == 8) {
        memcpy(buf, devEui, 8);
    } else {
        memcpy_P(buf, DEVEUI, 8);
    }
}

void os_getDevKey(u1_t *buf) {
    uint8_t appKey[16];

    if (EEPROM.readBytes(ADDR_APPKEY, appKey, 16) == 16) {
        memcpy(buf, appKey, 16);
    } else {
        memcpy_P(buf, APPKEY, 16);
    }
}

void do_send(osjob_t *j) {
    if (joinStatus == EV_JOINING) {
        DEBUG_PRINTF_TS("[LoRaWAN] Not joined yet\n");
        // Check if there is not a current TX/RX job running
        os_setTimedCallback(&sendjob, os_getTime() + sec2osticks(TX_INTERVAL), do_send);
        led1.setOffAfter(CRGB::Yellow, 500);
    } else if (LMIC.opmode & OP_TXRXPEND) {
        DEBUG_PRINTF_TS("[LoRaWAN] OP_TXRXPEND, not sending\n");
        led1.setOffAfter(CRGB::Red, 500);
    } else {
        DEBUG_PRINTF_TS("[LoRaWAN] OP_TXRXPEND,sending ...\n");
        led1.setOffAfter(CRGB::Blue, 500);

        byte loraData[12];
        LoraEncoder encoder(loraData);
        encoder.writeUnixtime(mySensor.unix_time);
        encoder.writeTemperature(mySensor.temperature_deg_c);
        encoder.writeUint16(mySensor.current_m_a);
        encoder.writeUint8(mySensor.voltage_v);
        encoder.writeUint8(mySensor.light_level);
        encoder.writeUint8(mySensor.status);
        encoder.writeUint8(mySensor.dimmer);

        // Prepare upstream data transmission at the next possible time.
        LMIC_setTxData2(1, loraData, sizeof(loraData), 0);
        os_setTimedCallback(&sendjob, os_getTime() + sec2osticks(TX_INTERVAL), do_send);
    }
}

void onEvent(ev_t ev) {
    switch (ev) {
        case EV_TXCOMPLETE:
            DEBUG_PRINTF_TS("[LoRaWAN] EV_TXCOMPLETE, rssi: %d, snr: %d\n", LMIC.rssi, LMIC.snr);
            led1.setOffAfter(CRGB::Green, 1000);

            if (LMIC.txrxFlags & TXRX_ACK) {
                DEBUG_PRINTF_TS("[LoRaWAN] Received ack\n");
            }

            if (LMIC.dataLen) {
                // data received in rx slot after tx
                DEBUG_PRINTF_TS("[LoRaWAN] Data Received: %d bytes, ", LMIC.dataLen);

                if (LMIC.dataLen) {
                    for (int i = 0; i < LMIC.dataLen; i++) {
                        DEBUG_PRINTF_TS("%02X ", LMIC.frame[LMIC.dataBeg + i]);
                    }
                    DEBUG_PRINTF("\n");

                    uint8_t method = LMIC.frame[LMIC.dataBeg + 0];
                    switch (method) {
                        case 0x00:
                            DEBUG_PRINTF_TS("[LoRaWAN] Command: 0x00 -> On/Off\n");
                            mySensor.status = LMIC.frame[LMIC.dataBeg + 1] > 0 ? true : false;
                            break;
                        case 0x01:
                            DEBUG_PRINTF_TS("[LoRaWAN] Command: 0x01 -> Dimmer\n");
                            mySensor.dimmer = LMIC.frame[LMIC.dataBeg + 1];
                            break;
                        default:
                            break;
                    }
                }
            }
            // Schedule next transmission
            os_setTimedCallback(&sendjob, os_getTime() + sec2osticks(TX_INTERVAL), do_send);
            break;
        case EV_JOINING:
            DEBUG_PRINTF_TS("[LoRaWAN] EV_JOINING: -> Joining...\n");
            led1.setFade(COLOR::BLUE, 750, 500);
            joinStatus = EV_JOINING;

            break;
        case EV_JOIN_FAILED:
            DEBUG_PRINTF_TS("[LoRaWAN] EV_JOIN_FAILED: -> Joining failed\n");
            led1.setOffAfter(CRGB::Red, 1000);

            break;
        case EV_JOINED:
            DEBUG_PRINTF_TS("[LoRaWAN] EV_JOINED\n");
            led1.setOffAfter(CRGB::AntiqueWhite, 1000);
            joinStatus = EV_JOINED;

            delay(3);
            // Disable link check validation (automatically enabled
            // during join, but not supported by TTN at this time).
            LMIC_setLinkCheckMode(0);

            break;
        case EV_RXCOMPLETE:
            // data received in ping slot
            DEBUG_PRINTF_TS("[LoRaWAN] EV_RXCOMPLETE\n");
            break;
        case EV_LINK_DEAD:
            DEBUG_PRINTF_TS("[LoRaWAN] EV_LINK_DEAD\n");
            break;
        case EV_LINK_ALIVE:
            DEBUG_PRINTF_TS("[LoRaWAN] EV_LINK_ALIVE\n");
            break;
        default:
            DEBUG_PRINTF_TS("[LoRaWAN] Unknown event\n");
            break;
    }
}

void setupLMIC(void) {
    // LMIC init
    os_init();

    // Reset the MAC state. Session and pending data transfers will be discarded.
    LMIC_reset();

    LMIC_setClockError(MAX_CLOCK_ERROR * 1 / 100);
    // Set up the channels used by the Things Network, which corresponds
    // to the defaults of most gateways. Without this, only three base
    // channels from the LoRaWAN specification are used, which certainly
    // works, so it is good for debugging, but can overload those
    // frequencies, so be sure to configure the full frequency range of
    // your network here (unless your network autoconfigures them).
    // Setting up channels should happen after LMIC_setSession, as that
    // configures the minimal channel set.

    LMIC_setupChannel(0, 868100000, DR_RANGE_MAP(DR_SF12, DR_SF7), BAND_CENTI);   // g-band
    LMIC_setupChannel(1, 868300000, DR_RANGE_MAP(DR_SF12, DR_SF7B), BAND_CENTI);  // g-band
    LMIC_setupChannel(2, 868500000, DR_RANGE_MAP(DR_SF12, DR_SF7), BAND_CENTI);   // g-band
    LMIC_setupChannel(3, 867100000, DR_RANGE_MAP(DR_SF12, DR_SF7), BAND_CENTI);   // g-band
    LMIC_setupChannel(4, 867300000, DR_RANGE_MAP(DR_SF12, DR_SF7), BAND_CENTI);   // g-band
    LMIC_setupChannel(5, 867500000, DR_RANGE_MAP(DR_SF12, DR_SF7), BAND_CENTI);   // g-band
    LMIC_setupChannel(6, 867700000, DR_RANGE_MAP(DR_SF12, DR_SF7), BAND_CENTI);   // g-band
    LMIC_setupChannel(7, 867900000, DR_RANGE_MAP(DR_SF12, DR_SF7), BAND_CENTI);   // g-band
    LMIC_setupChannel(8, 868800000, DR_RANGE_MAP(DR_FSK, DR_FSK), BAND_MILLI);    // g2-band

    // TTN defines an additional channel at 869.525Mhz using SF9 for class B
    // devices' ping slots. LMIC does not have an easy way to define set this
    // frequency and support for class B is spotty and untested, so this
    // frequency is not configured here.

    // Disable link check validation
    LMIC_setLinkCheckMode(0);

    // TTN uses SF9 for its RX2 window.
    LMIC.dn2Dr = DR_SF9;

    // Set data rate and transmit power for uplink (note: txpow seems to be ignored by the library)
    LMIC_setDrTxpow(spreadFactor, 14);

    // Start job
    LMIC_startJoining();

    do_send(&sendjob);  // Will fire up also the join
}

void loopLMIC(void) {
    os_runloop_once();
}
