farisrfp/smart-pju-device/firmware/src/boards.cpp

#include "boards.h"

// Global Object/Variable
cSensor mySensor;

// Sensor Variables
RTC_DS3231 rtc;
ACS712 acs712(ACS712_05B, ADC_CURRENT);
ZMPT101B zmpt101b(ADC_VOLTAGE, 50.0);

CRGB leds[NUM_LEDS];
LEDTask led1(0);
LEDTask led2(1);

void initBoard() {
    // Initialize EEPROM
    if (!EEPROM.begin(EEPROM_SIZE)) {
        DEBUG_PRINTF("Failed to initialise EEPROM\n");
        while (1)
            ;
    }

    // EEPROM.writeUShort(ADDR_CURRENT, ACS712_ZP);
    // EEPROM.writeUShort(ADDR_VOLTAGE, VOLTAGE_SENSITIVITY);
    // EEPROM.commit();

    pinMode(LED_BOARD, OUTPUT);
    pinMode(RELAY_PIN, OUTPUT);
    // DIMER PIN as PWM Pin
    ledcSetup(0, 1000, 8);
    ledcAttachPin(DIMMER_PIN, 0);

    SPI.begin(SPI_SCLK, SPI_MISO, SPI_MOSI);

    FastLED.addLeds<WS2812B, WS2812B_PIN, GRB>(leds, NUM_LEDS);
    FastLED.setBrightness(BRIGHTNESS);

    // Turn status on
    digitalWrite(RELAY_PIN, LOW);

    led1.setFlicker(CRGB::Red, 100, 100);
    led2.setFlicker(CRGB::Blue, 100, 100);
    delay(600);
    led1.setFlicker(CRGB::Orange, 100, 100);
    led2.setFlicker(CRGB::HotPink, 100, 100);
    delay(600);
    led1.turnOff();
    led2.turnOff();
}
