farisrfp/smart-pju-device/firmware/src/LoRaWAN/secrets.h

#ifndef SECRETS
#define SECRETS

// Chose LSB mode on the console and then copy it here.
// 1111111111111111
static const u1_t PROGMEM APPEUI[8] = {0x11, 0x11, 0x11, 0x11, 0x11, 0x11,0x11, 0x11};
// LSB mode
// 0x24, 0xE1, 0x05, 0xD0, 0x7E, 0xD5, 0xB3, 0x70
static const u1_t PROGMEM DEVEUI[8] = {0x24, 0xE1, 0x05, 0xD0, 0x7E, 0xD5, 0xB3, 0x70};
// MSB mode
// 8363A5BC1584D006D5595DEBAC3A2ED7
static const u1_t PROGMEM APPKEY[16] = {
    0x83, 0x63, 0xA5, 0xBC, 0x15, 0x84, 0xD0, 0x06, 0xD5, 0x59, 0x5D, 0xEB, 0xAC, 0x3A, 0x2E, 0xD7};

#endif
